xnvi/action_2_poor/doc/datasheet/lcd_pin_def.jpg

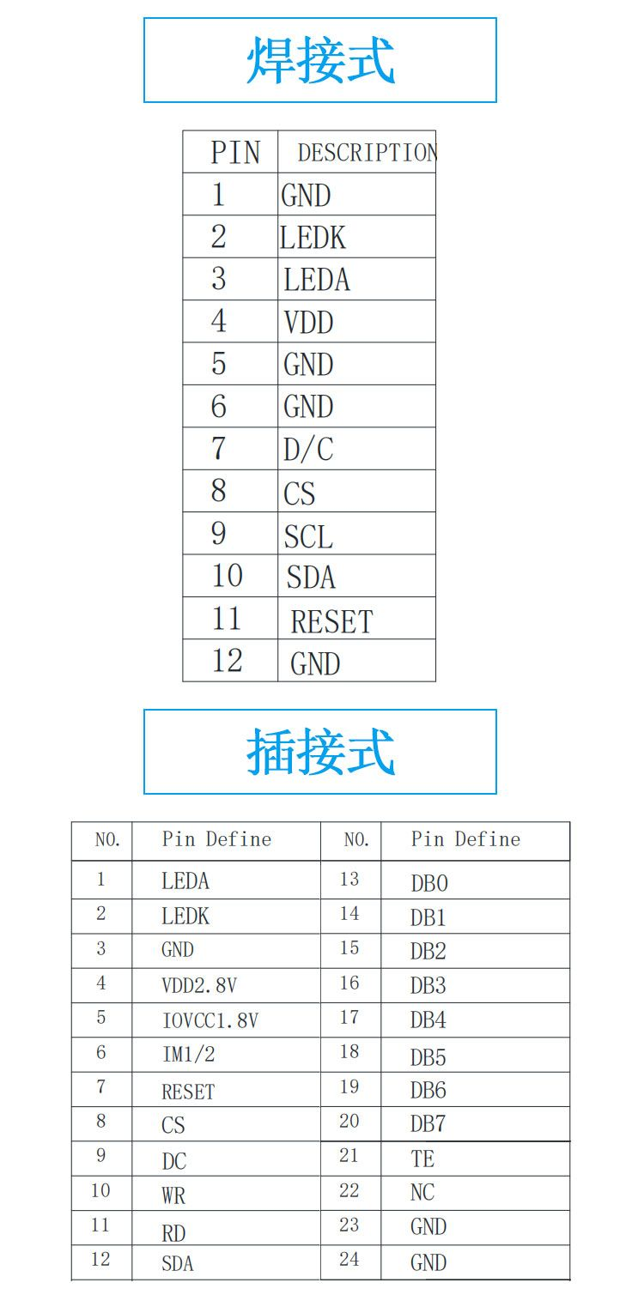
doc/datasheet/lcd_pin_def.jpg
