xnvi/action_2_poor/doc/datasheet/lcd_screen_struct.jpg

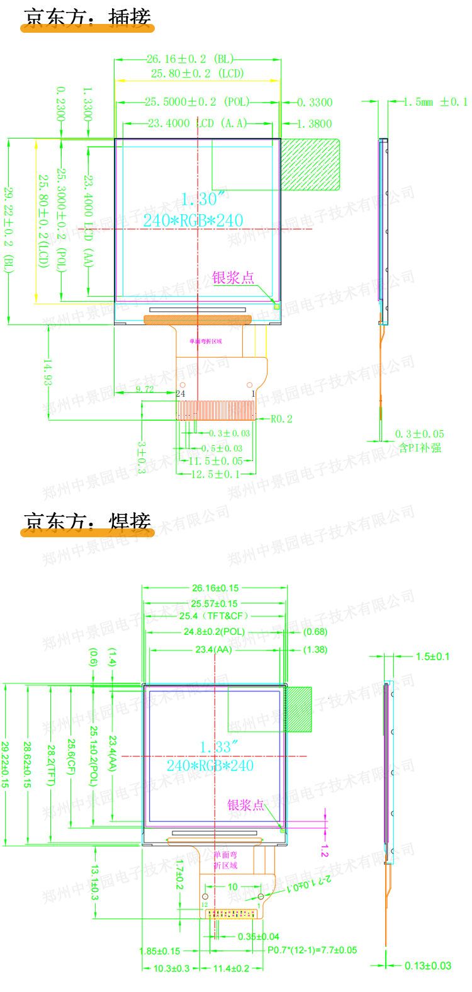
doc/datasheet/lcd_screen_struct.jpg
