xnvi/action_2_poor/doc/datasheet/ov5640_fov67.jpg

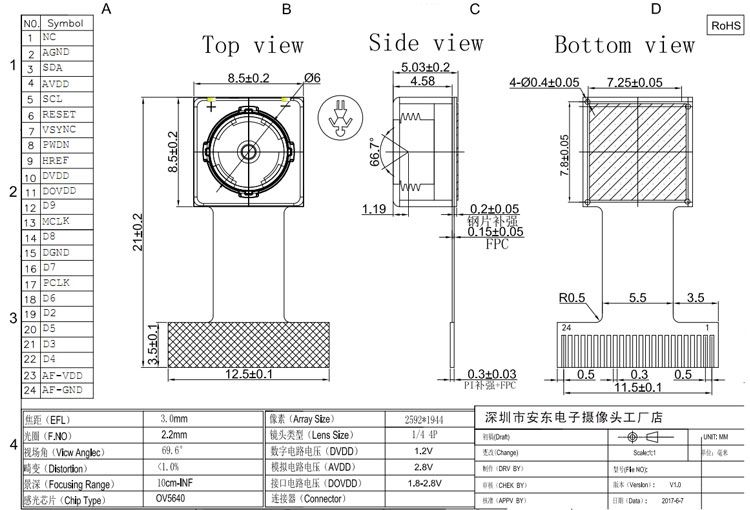
doc/datasheet/ov5640_fov67.jpg
