xnvi/action_2_poor/doc/datasheet/ov5640_fov96.jpg

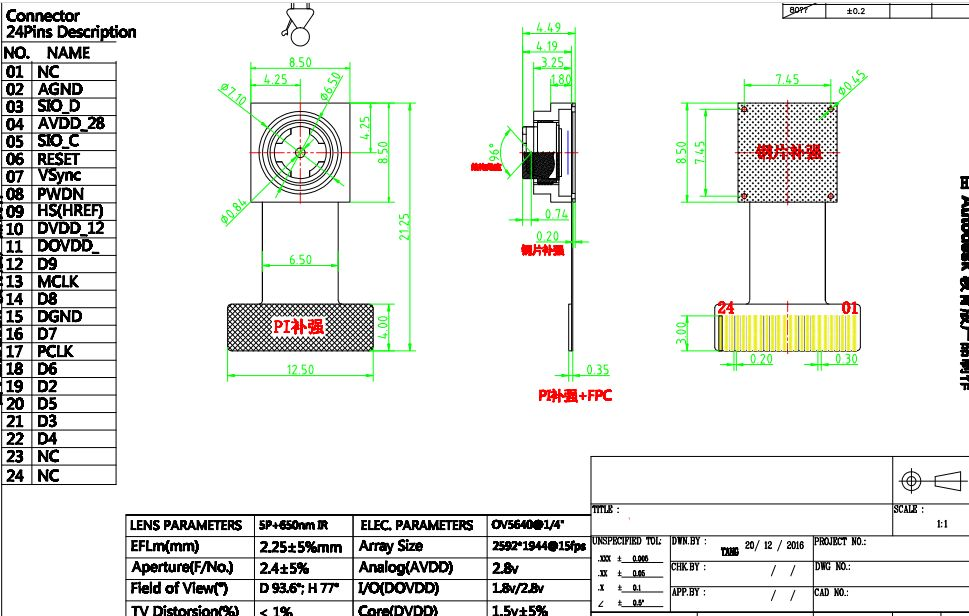
doc/datasheet/ov5640_fov96.jpg
