xnvi/action_2_poor/doc/datasheet/touch_screen.jpg

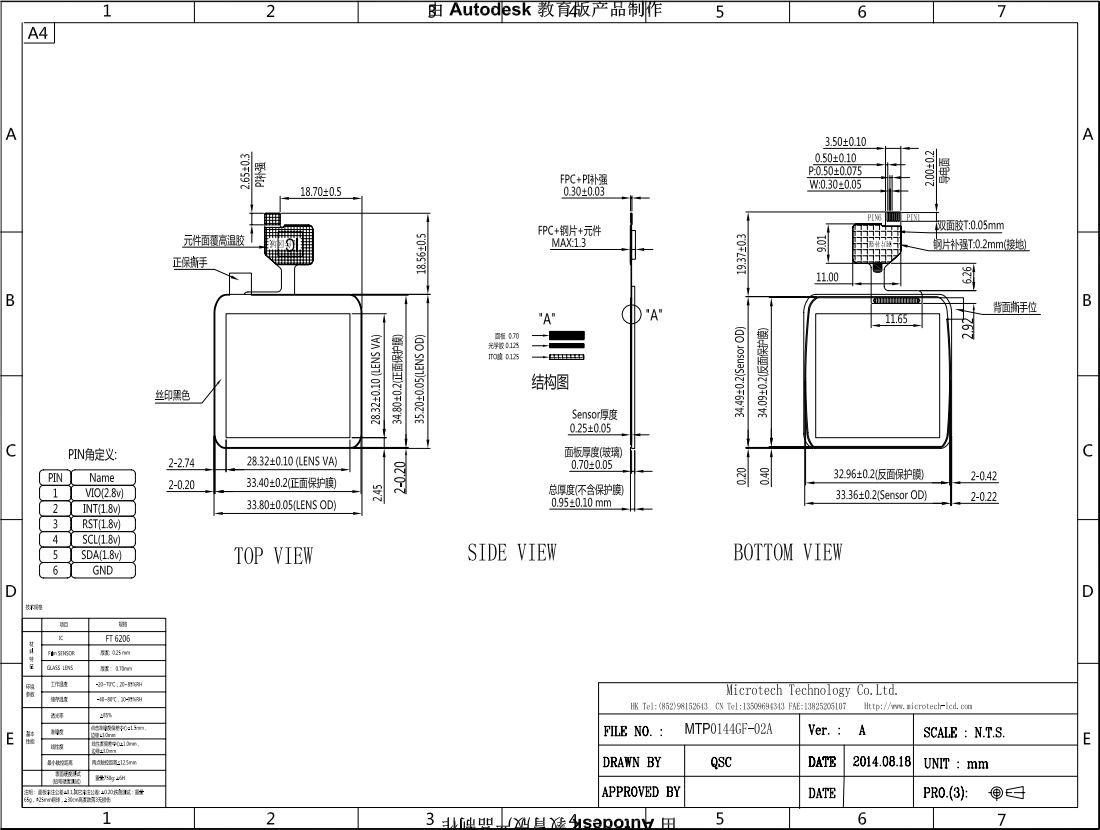
doc/datasheet/touch_screen.jpg
