xnvi/action_2_poor/software/app/camera/src/himpp_venc.c

/******************************************************************************

  Copyright (C), 2017, Hisilicon Tech. Co., Ltd.

 ******************************************************************************
  File Name     : sample_comm_venc.c
  Version       : Initial Draft
  Author        : Hisilicon multimedia software group
  Created       : 2017
  Description   :
******************************************************************************/


#ifdef __cplusplus
#if __cplusplus
extern "C" {
#endif
#endif /* End of #ifdef __cplusplus */

#include <stdio.h>
#include <stdlib.h>
#include <string.h>
#include <sys/types.h>
#include <sys/stat.h>
#include <sys/ioctl.h>
#include <sys/poll.h>
#include <sys/time.h>
#include <sys/select.h>
#include <fcntl.h>
#include <errno.h>
#include <pthread.h>
#include <math.h>
#include <unistd.h>
#include <signal.h>
#include <sys/prctl.h>

#include "himpp.h"

// my edit
#include "camera_himpp_config.h"

const HI_U8 g_SOI[2] = {0xFF, 0xD8};
const HI_U8 g_EOI[2] = {0xFF, 0xD9};
static pthread_t gs_VencPid;
static pthread_t gs_VencQpmapPid;
static HIMPP_VENC_GETSTREAM_PARA_S gs_stPara;
static HIMPP_VENC_QPMAP_SENDFRAME_PARA_S stQpMapSendFramePara;

static HI_S32 gs_s32SnapCnt = 0;
HI_CHAR* DstBuf = NULL;
#define TEMP_BUF_LEN 8
#define MAX_THM_SIZE (64*1024)

// my edit
extern HI_S32 get_hisi_video_frame(VENC_CHN VencChn, VENC_STREAM_S* pstStream);

#ifdef __READ_ALL_FILE__
static HI_S32 FileTrans_GetThmFromJpg(HI_CHAR* JPGPath, HI_U32* DstSize)
{
    HI_S32 s32RtnVal = 0;
    FILE* fpJpg = NULL;
    HI_CHAR tempbuf[TEMP_BUF_LEN] = {0};
    HI_S32 bufpos = 0;
    HI_CHAR startflag[2] = {0xff, 0xd8};
    HI_S32 startpos = 0;
    HI_CHAR endflag[2] = {0xff, 0xd9};
    HI_S32 endpos = 0;
    fpJpg = fopen(JPGPath, "rb");
    HI_CHAR* pszFile = NULL;
    HI_S32 fd = 0;
    HI_S32 s32I = 0;
    struct stat stStat;
    memset(&stStat, 0, sizeof(struct stat));
    if (NULL == fpJpg)
    {
        printf("file %s not exist!\n", JPGPath);
        return HI_FAILURE;
    }
    else
    {
        fd = fileno(fpJpg);
        fstat(fd, &stStat);
        pszFile = (HI_CHAR*)malloc(stStat.st_size);
        if ((NULL == pszFile) || (stStat.st_size < 6))
        {
            fclose(fpJpg);
            printf("memory malloc fail!\n");
            return HI_FAILURE;
        }

        if (fread(pszFile, stStat.st_size , 1, fpJpg) <= 0)
        {
            fclose(fpJpg);
            free(pszFile);
            printf("fread jpeg src fail!\n");
            return HI_FAILURE;
        }

        fclose(fpJpg);
        HI_U16 u16THMLen = 0;
        u16THMLen = (pszFile[4] << 8) + pszFile[5];
        while (s32I < stStat.st_size)
        {
            tempbuf[bufpos] = pszFile[s32I++];
            if (bufpos > 0)
            {
                if (0 == memcmp(tempbuf + bufpos - 1, startflag, sizeof(startflag)))
                {
                    startpos = s32I - 2;
                    if (startpos < 0)
                    {
                        startpos = 0;
                    }
                }
                if (0 == memcmp(tempbuf + bufpos - 1, endflag, sizeof(endflag)))
                {
                    if (u16THMLen == s32I)
                    {
                        endpos = s32I;
                        break;
                    }
                    else
                    {
                        endpos = s32I;
                        break;
                    }
                }
            }
            bufpos++;
            if (bufpos == (TEMP_BUF_LEN - 1))
            {
                if (tempbuf[bufpos - 1] != 0xFF)
                {
                    bufpos = 0;
                }

            }
            else if (bufpos > (TEMP_BUF_LEN - 1))
            {
                bufpos = 0;
            }

        }

    }
    if (endpos - startpos <= 0)
    {
        free(pszFile);
        printf("get .thm 11 fail!\n");
        return HI_FAILURE;
    }

    if (endpos - startpos >= stStat.st_size)
    {
        free(pszFile);
        printf("NO DCF info, get .thm 22 fail!\n");
        return HI_FAILURE;
    }

    HI_CHAR* temp = pszFile + startpos;
    if(MAX_THM_SIZE < (endpos - startpos))
    {
        printf("Thm is too large than MAX_THM_SIZE, get .thm 33 fail!\n");
        return HI_FAILURE;
    }

    HI_CHAR* cDstBuf = (HI_CHAR*)malloc(endpos - startpos);
    if (NULL == cDstBuf)
    {
        printf("memory malloc fail!\n");
        return HI_FAILURE;
    }

    memcpy(cDstBuf, temp, endpos - startpos);

    DstBuf = cDstBuf;
    *DstSize = endpos - startpos;
    free(pszFile);

    return HI_SUCCESS;
}

#else
static HI_S32 FileTrans_GetThmFromJpg(HI_CHAR* JPGPath, HI_U32* DstSize)
{
    HI_CHAR tempbuf[TEMP_BUF_LEN] = {0};
    HI_S32 bufpos = 0;
    HI_CHAR startflag[2] = {0xff, 0xd8};
    HI_S32 startpos = 0;
    HI_CHAR endflag[2] = {0xff, 0xd9};
    HI_S32 endpos = 0;
    HI_BOOL bStartMatch = HI_FALSE;

    HI_S32 fd = 0;
    struct stat stStat;
    memset(&stStat, 0, sizeof(struct stat));

    FILE* fpJpg = NULL;
    fpJpg = fopen(JPGPath, "rb");
    if (NULL == fpJpg)
    {
        printf("file %s not exist!\n", JPGPath);
        return HI_FAILURE;
    }
    else
    {
        fd = fileno(fpJpg);
        fstat(fd, &stStat);

        while (!feof(fpJpg))
        {
            tempbuf[bufpos]=getc(fpJpg);
            if (bufpos > 0)
            {
                if (0 == memcmp(tempbuf + bufpos - 1, startflag, sizeof(startflag)))
                {
                    startpos = ftell(fpJpg)-2;
                    if (startpos < 0)
                    {
                        startpos = 0;
                    }
                    bStartMatch = HI_TRUE;
                }
                if (0 == memcmp(tempbuf + bufpos - 1, endflag, sizeof(endflag)))
                {
                    endpos = ftell(fpJpg);
                    if(HI_TRUE == bStartMatch)
                    {
                        break;
                    }
                }
            }
            bufpos++;

            if (bufpos == (TEMP_BUF_LEN - 1))
            {
                if (tempbuf[bufpos - 1] != 0xFF)
                {
                    bufpos = 0;
                }
            }
            else if (bufpos > (TEMP_BUF_LEN - 1))
            {
                if (tempbuf[bufpos -1] == 0xFF)
                {
                    tempbuf[0] = 0xFF;
                    bufpos = 1;
                }
                else
                {
                    bufpos = 0;
                }
            }
        }
    }

    if (endpos - startpos <= 0)
    {
        printf("get .thm 11 fail!\n");
        fclose(fpJpg);
        return HI_FAILURE;
    }

    if (endpos - startpos > MAX_THM_SIZE)
    {
        printf("Thm is too large than MAX_THM_SIZE, get .thm 22 fail!\n");
        fclose(fpJpg);
        return HI_FAILURE;
    }

    if (endpos - startpos >= stStat.st_size)
    {
        printf("NO DCF info, get .thm 33 fail!\n");
        fclose(fpJpg);
        return HI_FAILURE;
    }

    HI_CHAR* cDstBuf = (HI_CHAR*)malloc(endpos - startpos);
    if (NULL == cDstBuf)
    {
        printf("memory malloc fail!\n");
        fclose(fpJpg);
        return HI_FAILURE;
    }

    fseek(fpJpg, (long)startpos, SEEK_SET);
    *DstSize = fread(cDstBuf,1,endpos-startpos,fpJpg);
    if(*DstSize != (endpos - startpos))
    {
        free(cDstBuf);
        printf("fread fail!\n");
        fclose(fpJpg);
        return HI_FAILURE;
    }

    DstBuf = cDstBuf;
    fclose(fpJpg);

    return HI_SUCCESS;
}
#endif


/******************************************************************************
* funciton : get file postfix according palyload_type.
******************************************************************************/
HI_S32 HIMPP_VENC_GetFilePostfix(PAYLOAD_TYPE_E enPayload, char* szFilePostfix)
{
    if (PT_H264 == enPayload)
    {
        strcpy(szFilePostfix, ".h264");
    }
    else if (PT_H265 == enPayload)
    {
        strcpy(szFilePostfix, ".h265");
    }
    else if (PT_JPEG == enPayload)
    {
        strcpy(szFilePostfix, ".jpg");
    }
    else if (PT_MJPEG == enPayload)
    {
        strcpy(szFilePostfix, ".mjp");
    }
    else
    {
        HIMPP_PRT("payload type err!\n");
        return HI_FAILURE;
    }
    return HI_SUCCESS;
}


HI_S32 HIMPP_VENC_GetGopAttr(VENC_GOP_MODE_E enGopMode,VENC_GOP_ATTR_S *pstGopAttr)
{
    switch(enGopMode)
    {
        case VENC_GOPMODE_NORMALP:
            pstGopAttr->enGopMode  = VENC_GOPMODE_NORMALP;
            pstGopAttr->stNormalP.s32IPQpDelta = 2;
        break;
        case VENC_GOPMODE_SMARTP:
            pstGopAttr->enGopMode  = VENC_GOPMODE_SMARTP;
            pstGopAttr->stSmartP.s32BgQpDelta  = 4;
            pstGopAttr->stSmartP.s32ViQpDelta  = 2;
            pstGopAttr->stSmartP.u32BgInterval =  90;
        break;

        case VENC_GOPMODE_DUALP:
            pstGopAttr->enGopMode  = VENC_GOPMODE_DUALP;
            pstGopAttr->stDualP.s32IPQpDelta  = 4;
            pstGopAttr->stDualP.s32SPQpDelta  = 2;
            pstGopAttr->stDualP.u32SPInterval = 3;
        break;

        case VENC_GOPMODE_BIPREDB:
            pstGopAttr->enGopMode  = VENC_GOPMODE_BIPREDB;
            pstGopAttr->stBipredB.s32BQpDelta  = -2;
            pstGopAttr->stBipredB.s32IPQpDelta = 3;
            pstGopAttr->stBipredB.u32BFrmNum   = 2;
        break;

        default:
            HIMPP_PRT("not support the gop mode !\n");
            return HI_FAILURE;
        break;
    }
    return HI_SUCCESS;
}


HI_S32 HIMPP_VENC_Getdcfinfo(char* SrcJpgPath, char* DstThmPath)
{
    HI_S32 s32RtnVal = HI_SUCCESS;
    HI_CHAR JPGSrcPath[FILE_NAME_LEN] = {0};
    HI_CHAR JPGDesPath[FILE_NAME_LEN] = {0};
    HI_U32 DstSize = 0;
    snprintf(JPGSrcPath, sizeof(JPGSrcPath), "%s", SrcJpgPath);
    snprintf(JPGDesPath, sizeof(JPGDesPath), "%s", DstThmPath);

    s32RtnVal = FileTrans_GetThmFromJpg(JPGSrcPath, &DstSize);
    if ((HI_SUCCESS != s32RtnVal) || (0 == DstSize))
    {
        printf("fail to get thm\n");
        return HI_FAILURE;
    }

    FILE* fpTHM = fopen(JPGDesPath, "w");
    if (HI_NULL == fpTHM)
    {
        printf("file to create file %s\n", JPGDesPath);
        return HI_FAILURE;
    }

    HI_U32 u32WritenSize = 0;
    while (u32WritenSize < DstSize)
    {
        s32RtnVal = fwrite(DstBuf + u32WritenSize, 1, DstSize, fpTHM);
        if (s32RtnVal <= 0)
        {
            printf("fail to wirte file, rtn=%d\n", s32RtnVal);
            break;
        }

        u32WritenSize += s32RtnVal;
    }

    if (fpTHM)
    {
        fclose(fpTHM);
        fpTHM = 0;
    }

    if(NULL != DstBuf)
    {
        free(DstBuf);
        DstBuf = NULL;
    }

    return 0;
}



/******************************************************************************
* funciton : save stream
******************************************************************************/
HI_S32 HIMPP_VENC_SaveStream(FILE* pFd, VENC_STREAM_S* pstStream)
{
    HI_S32 i;

    for (i = 0; i < pstStream->u32PackCount; i++)
    {
        fwrite(pstStream->pstPack[i].pu8Addr + pstStream->pstPack[i].u32Offset,
               pstStream->pstPack[i].u32Len - pstStream->pstPack[i].u32Offset, 1, pFd);

        fflush(pFd);
    }

    return HI_SUCCESS;
}


/******************************************************************************
* funciton : the process of physical address retrace
******************************************************************************/
HI_S32 HIMPP_VENC_SaveStream_PhyAddr(FILE* pFd, VENC_STREAM_BUF_INFO_S *pstStreamBuf, VENC_STREAM_S* pstStream)
{
    HI_U32 i,j;
    HI_U64 u64SrcPhyAddr;
    HI_U32 u32Left;
    HI_S32 s32Ret = 0;

    for(i=0; i<pstStream->u32PackCount; i++)
    {
        for(j=0; j<MAX_TILE_NUM; j++)
        {
            if((pstStream->pstPack[i].u64PhyAddr > pstStreamBuf->u64PhyAddr[j])&&\
                (pstStream->pstPack[i].u64PhyAddr <= pstStreamBuf->u64PhyAddr[j]+pstStreamBuf->u64BufSize[j]))
                break;
        }

        if(pstStream->pstPack[i].u64PhyAddr + pstStream->pstPack[i].u32Len >=
                pstStreamBuf->u64PhyAddr[j] + pstStreamBuf->u64BufSize[j])
        {
            if (pstStream->pstPack[i].u64PhyAddr + pstStream->pstPack[i].u32Offset >=
                pstStreamBuf->u64PhyAddr[j] + pstStreamBuf->u64BufSize[j])
            {
                /* physical address retrace in offset segment */
                u64SrcPhyAddr = pstStreamBuf->u64PhyAddr[j] +
                                ((pstStream->pstPack[i].u64PhyAddr + pstStream->pstPack[i].u32Offset) -
                                (pstStreamBuf->u64PhyAddr[j] + pstStreamBuf->u64BufSize[j]));

                s32Ret = fwrite ((void *)(HI_UL)u64SrcPhyAddr, pstStream->pstPack[i].u32Len - pstStream->pstPack[i].u32Offset, 1, pFd);
                if(s32Ret<0)
                {
                    HIMPP_PRT("fwrite err %d\n", s32Ret);
                    return s32Ret;
                }
            }
            else
            {
                /* physical address retrace in data segment */
                u32Left = (pstStreamBuf->u64PhyAddr[j] + pstStreamBuf->u64BufSize[j]) - pstStream->pstPack[i].u64PhyAddr;

                s32Ret = fwrite((void *)(HI_UL)(pstStream->pstPack[i].u64PhyAddr + pstStream->pstPack[i].u32Offset),
                             u32Left - pstStream->pstPack[i].u32Offset, 1, pFd);
                if(s32Ret<0)
                {
                    HIMPP_PRT("fwrite err %d\n", s32Ret);
                    return s32Ret;
                }

                s32Ret = fwrite((void *)(HI_UL)pstStreamBuf->u64PhyAddr[j], pstStream->pstPack[i].u32Len - u32Left, 1, pFd);
                if(s32Ret<0)
                {
                    HIMPP_PRT("fwrite err %d\n", s32Ret);
                    return s32Ret;
                }
            }
        }
        else
        {
            /* physical address retrace does not happen */
            s32Ret = fwrite ((void *)(HI_UL)(pstStream->pstPack[i].u64PhyAddr + pstStream->pstPack[i].u32Offset),
                          pstStream->pstPack[i].u32Len - pstStream->pstPack[i].u32Offset, 1, pFd);
            if(s32Ret<0)
            {
                HIMPP_PRT("fwrite err %d\n", s32Ret);
                return s32Ret;
            }
        }
            fflush(pFd);
    }
    return HI_SUCCESS;
}

HI_S32 HIMPP_VENC_CloseReEncode(VENC_CHN VencChn)
{
    HI_S32 s32Ret;
    VENC_RC_PARAM_S stRcParam;
    VENC_CHN_ATTR_S stChnAttr;

    s32Ret = HI_MPI_VENC_GetChnAttr(VencChn,&stChnAttr);
    if (HI_SUCCESS != s32Ret)
    {
        HIMPP_PRT("GetChnAttr failed!\n");
        return HI_FAILURE;
    }

    s32Ret = HI_MPI_VENC_GetRcParam(VencChn,&stRcParam);
    if (HI_SUCCESS != s32Ret)
    {
        HIMPP_PRT("GetRcParam failed!\n");
        return HI_FAILURE;
    }

    if(VENC_RC_MODE_H264CBR == stChnAttr.stRcAttr.enRcMode)
    {
        stRcParam.stParamH264Cbr.s32MaxReEncodeTimes = 0;
    }
    else if(VENC_RC_MODE_H264VBR == stChnAttr.stRcAttr.enRcMode)
    {
        stRcParam.stParamH264Vbr.s32MaxReEncodeTimes = 0;
    }
    else if(VENC_RC_MODE_H265CBR == stChnAttr.stRcAttr.enRcMode)
    {
        stRcParam.stParamH264Cbr.s32MaxReEncodeTimes = 0;
    }
    else if(VENC_RC_MODE_H265VBR == stChnAttr.stRcAttr.enRcMode)
    {
        stRcParam.stParamH264Vbr.s32MaxReEncodeTimes = 0;
    }
    else
    {
        return HI_SUCCESS;
    }
    s32Ret = HI_MPI_VENC_SetRcParam(VencChn,&stRcParam);
    if (HI_SUCCESS != s32Ret)
    {
        HIMPP_PRT("SetRcParam failed!\n");
        return HI_FAILURE;
    }
    return HI_SUCCESS;
}

HI_S32 HIMPP_VENC_Creat(VENC_CHN VencChn, PAYLOAD_TYPE_E enType,  PIC_SIZE_E enSize, HIMPP_RC_E enRcMode, HI_U32  u32Profile, HI_BOOL bRcnRefShareBuf,VENC_GOP_ATTR_S *pstGopAttr)
{
    HI_S32 s32Ret;
    SIZE_S stPicSize;
    VENC_CHN_ATTR_S        stVencChnAttr;
    VENC_ATTR_JPEG_S       stJpegAttr;
    HIMPP_VI_CONFIG_S     stViConfig;
    HI_U32                 u32FrameRate;
    HI_U32                 u32StatTime;
    HI_U32                 u32Gop = 30;

    s32Ret = HIMPP_SYS_GetPicSize( enSize, &stPicSize);
    if (HI_SUCCESS != s32Ret)
    {
        HIMPP_PRT("Get picture size failed!\n");
        return HI_FAILURE;
    }

    HIMPP_VI_GetSensorInfo(&stViConfig);
    if(HIMPP_SNS_TYPE_BUTT == stViConfig.astViInfo[0].stSnsInfo.enSnsType)
    {
        HIMPP_PRT("Not set SENSOR%d_TYPE !\n",0);
        return HI_FALSE;
    }
    s32Ret = HIMPP_VI_GetFrameRateBySensor(stViConfig.astViInfo[0].stSnsInfo.enSnsType, &u32FrameRate);
    if (HI_SUCCESS != s32Ret)
    {
        HIMPP_PRT("HIMPP_VI_GetFrameRateBySensor failed!\n");
        return s32Ret;
    }

    /******************************************
     step 1:  Create Venc Channel
    ******************************************/
    stVencChnAttr.stVencAttr.enType          = enType;
    stVencChnAttr.stVencAttr.u32MaxPicWidth  = stPicSize.u32Width;
    stVencChnAttr.stVencAttr.u32MaxPicHeight = stPicSize.u32Height;
    stVencChnAttr.stVencAttr.u32PicWidth     = stPicSize.u32Width;/*the picture width*/
    stVencChnAttr.stVencAttr.u32PicHeight    = stPicSize.u32Height;/*the picture height*/

    if (enType == PT_MJPEG || enType == PT_JPEG)
    {
        stVencChnAttr.stVencAttr.u32BufSize      = ALIGN_UP(stPicSize.u32Width, 16) * ALIGN_UP(stPicSize.u32Height, 16);
    }
    else
    {
        stVencChnAttr.stVencAttr.u32BufSize      = ALIGN_UP(stPicSize.u32Width * stPicSize.u32Height * 3 / 4, 64);/*stream buffer size*/
    }
    stVencChnAttr.stVencAttr.u32Profile      = u32Profile;
    stVencChnAttr.stVencAttr.bByFrame        = HI_TRUE;/*get stream mode is slice mode or frame mode?*/

    if(VENC_GOPMODE_SMARTP == pstGopAttr->enGopMode)
    {
        u32StatTime = pstGopAttr->stSmartP.u32BgInterval/u32Gop;
    }
    else
    {
        u32StatTime = 1;
    }

    switch (enType)
    {
        case PT_H265:
        {
            if (HIMPP_RC_CBR == enRcMode)
            {
                VENC_H265_CBR_S    stH265Cbr;

                stVencChnAttr.stRcAttr.enRcMode = VENC_RC_MODE_H265CBR;
                stH265Cbr.u32Gop            = u32Gop;
                stH265Cbr.u32StatTime       = u32StatTime; /* stream rate statics time(s) */
                stH265Cbr.u32SrcFrameRate   = u32FrameRate; /* input (vi) frame rate */
                stH265Cbr.fr32DstFrameRate  = u32FrameRate; /* target frame rate */
                switch (enSize)
                {
                    // my edit 目前只使用cbr，这里通过码率设置图像质量
                    case PIC_VGA:
                        stH265Cbr.u32BitRate = (1024 + 512*u32FrameRate/30) * g_br_list[g_br_index].num/g_br_list[g_br_index].den;
                        break;
                    case PIC_720P:
                        stH265Cbr.u32BitRate = (1024 * 2 + 1024*u32FrameRate/30) * g_br_list[g_br_index].num/g_br_list[g_br_index].den;
                        break;
                    case PIC_1080P:
                        stH265Cbr.u32BitRate = (1024 * 2 + 2048*u32FrameRate/30) * g_br_list[g_br_index].num/g_br_list[g_br_index].den;
                        break;
                    case PIC_2592x1944:
                        stH265Cbr.u32BitRate = (1024 * 3 + 3072*u32FrameRate/30) * g_br_list[g_br_index].num/g_br_list[g_br_index].den;
                        break;
                    case PIC_3840x2160:
                        stH265Cbr.u32BitRate = (1024 * 5  + 5120*u32FrameRate/30) * g_br_list[g_br_index].num/g_br_list[g_br_index].den;
                        break;
                    default : //other small resolution
                        stH265Cbr.u32BitRate = 256;
                        break;
                }
                memcpy(&stVencChnAttr.stRcAttr.stH265Cbr, &stH265Cbr, sizeof(VENC_H265_CBR_S));
            }
            else if (HIMPP_RC_FIXQP == enRcMode)
            {
                VENC_H265_FIXQP_S    stH265FixQp;

                stVencChnAttr.stRcAttr.enRcMode = VENC_RC_MODE_H265FIXQP;
                stH265FixQp.u32Gop              = 30;
                stH265FixQp.u32SrcFrameRate     = u32FrameRate;
                stH265FixQp.fr32DstFrameRate    = u32FrameRate;
                stH265FixQp.u32IQp              = 25;
                stH265FixQp.u32PQp              = 30;
                stH265FixQp.u32BQp              = 32;
                memcpy(&stVencChnAttr.stRcAttr.stH265FixQp, &stH265FixQp, sizeof(VENC_H265_FIXQP_S));
            }
            else if (HIMPP_RC_VBR == enRcMode)
            {
                VENC_H265_VBR_S    stH265Vbr;

                stVencChnAttr.stRcAttr.enRcMode = VENC_RC_MODE_H265VBR;
                stH265Vbr.u32Gop           = u32Gop;
                stH265Vbr.u32StatTime      = u32StatTime;
                stH265Vbr.u32SrcFrameRate  = u32FrameRate;
                stH265Vbr.fr32DstFrameRate = u32FrameRate;
                switch (enSize)
                {
                    case PIC_VGA:
                        stH265Vbr.u32MaxBitRate = 1024 + 512*u32FrameRate/30;
                        break;
                    case PIC_720P:
                        stH265Vbr.u32MaxBitRate = 1024 * 2 + 1024*u32FrameRate/30;
                        break;
                    case PIC_1080P:
                        stH265Vbr.u32MaxBitRate = 1024 * 2 + 2048*u32FrameRate/30;
                        break;
                    case PIC_2592x1944:
                        stH265Vbr.u32MaxBitRate = 1024 * 3 + 3072*u32FrameRate/30;
                        break;
                    default :
                        stH265Vbr.u32MaxBitRate    = 1024 * 15 + 2048*u32FrameRate/30;
                        break;
                }
                memcpy(&stVencChnAttr.stRcAttr.stH265Vbr, &stH265Vbr, sizeof(VENC_H265_VBR_S));
            }
            else if(HIMPP_RC_AVBR == enRcMode)
            {
                VENC_H265_AVBR_S    stH265AVbr;

                stVencChnAttr.stRcAttr.enRcMode = VENC_RC_MODE_H265AVBR;
                stH265AVbr.u32Gop         = u32Gop;
                stH265AVbr.u32StatTime    = u32StatTime;
                stH265AVbr.u32SrcFrameRate  = u32FrameRate;
                stH265AVbr.fr32DstFrameRate = u32FrameRate;
                switch (enSize)
                {
                    case PIC_VGA:
                        stH265AVbr.u32MaxBitRate = 1024 + 512*u32FrameRate/30;
                        break;
                    case PIC_720P:
                        stH265AVbr.u32MaxBitRate = 1024 * 2 + 1024*u32FrameRate/30;
                        break;
                    case PIC_1080P:
                        stH265AVbr.u32MaxBitRate = 1024 * 2 + 2048*u32FrameRate/30;
                        break;
                    case PIC_2592x1944:
                        stH265AVbr.u32MaxBitRate = 1024 * 3 + 3072*u32FrameRate/30;
                        break;
                    case PIC_3840x2160:
                        stH265AVbr.u32MaxBitRate = 1024 * 5  + 5120*u32FrameRate/30;
                        break;
                    default :
                        stH265AVbr.u32MaxBitRate    = 1024 * 15 + 2048*u32FrameRate/30;
                        break;
                }
                memcpy(&stVencChnAttr.stRcAttr.stH265AVbr, &stH265AVbr, sizeof(VENC_H265_AVBR_S));
            }
            else if(HIMPP_RC_QVBR == enRcMode)
            {
                VENC_H265_QVBR_S    stH265QVbr;

                stVencChnAttr.stRcAttr.enRcMode = VENC_RC_MODE_H265QVBR;
                stH265QVbr.u32Gop         = u32Gop;
                stH265QVbr.u32StatTime    = u32StatTime;
                stH265QVbr.u32SrcFrameRate  = u32FrameRate;
                stH265QVbr.fr32DstFrameRate = u32FrameRate;
                switch (enSize)
                {
                    case PIC_VGA:
                        stH265QVbr.u32TargetBitRate = 1024 + 512*u32FrameRate/30;
                        break;
                    case PIC_720P:
                        stH265QVbr.u32TargetBitRate= 1024 * 2 + 1024*u32FrameRate/30;
                        break;
                    case PIC_1080P:
                        stH265QVbr.u32TargetBitRate = 1024 * 2 + 2048*u32FrameRate/30;
                        break;
                    case PIC_2592x1944:
                        stH265QVbr.u32TargetBitRate = 1024 * 3 + 3072*u32FrameRate/30;
                        break;
                    case PIC_3840x2160:
                        stH265QVbr.u32TargetBitRate = 1024 * 5  + 5120*u32FrameRate/30;
                        break;
                    case PIC_4000x3000:
                        stH265QVbr.u32TargetBitRate = 1024 * 10 + 5120*u32FrameRate/30;
                        break;
                    case PIC_7680x4320:
                        stH265QVbr.u32TargetBitRate = 1024 * 20 + 5120*u32FrameRate/30;
                        break;
                    default :
                        stH265QVbr.u32TargetBitRate    = 1024 * 15 + 2048*u32FrameRate/30;
                        break;
                }
                memcpy(&stVencChnAttr.stRcAttr.stH265QVbr, &stH265QVbr, sizeof(VENC_H265_QVBR_S));
            }
            else if(HIMPP_RC_CVBR == enRcMode)
            {
                VENC_H265_CVBR_S    stH265CVbr;

                stVencChnAttr.stRcAttr.enRcMode = VENC_RC_MODE_H265CVBR;
                stH265CVbr.u32Gop         = u32Gop;
                stH265CVbr.u32StatTime    = u32StatTime;
                stH265CVbr.u32SrcFrameRate  = u32FrameRate;
                stH265CVbr.fr32DstFrameRate = u32FrameRate;
                stH265CVbr.u32LongTermStatTime  = 1;
                stH265CVbr.u32ShortTermStatTime = u32StatTime;
                switch (enSize)
                {
                    case PIC_VGA:
                        stH265CVbr.u32MaxBitRate = 1024 + 512*u32FrameRate/30;
                        stH265CVbr.u32LongTermMaxBitrate = 1024  + 512*u32FrameRate/30;
                        stH265CVbr.u32LongTermMinBitrate = 256;
                        break;
                    case PIC_720P:
                        stH265CVbr.u32MaxBitRate         = 1024 * 3 + 1024*u32FrameRate/30;
                        stH265CVbr.u32LongTermMaxBitrate = 1024 * 2 + 1024*u32FrameRate/30;
                        stH265CVbr.u32LongTermMinBitrate = 512;
                        break;
                    case PIC_1080P:
                        stH265CVbr.u32MaxBitRate         = 1024 * 2 + 2048*u32FrameRate/30;
                        stH265CVbr.u32LongTermMaxBitrate = 1024 * 2 + 2048*u32FrameRate/30;
                        stH265CVbr.u32LongTermMinBitrate = 1024;
                        break;
                    case PIC_2592x1944:
                        stH265CVbr.u32MaxBitRate         = 1024 * 4 + 3072*u32FrameRate/30;
                        stH265CVbr.u32LongTermMaxBitrate = 1024 * 3 + 3072*u32FrameRate/30;
                        stH265CVbr.u32LongTermMinBitrate = 1024*2;
                        break;
                    case PIC_3840x2160:
                        stH265CVbr.u32MaxBitRate         = 1024 * 8  + 5120*u32FrameRate/30;
                        stH265CVbr.u32LongTermMaxBitrate = 1024 * 5  + 5120*u32FrameRate/30;
                        stH265CVbr.u32LongTermMinBitrate = 1024*3;
                        break;
                    case PIC_4000x3000:
                        stH265CVbr.u32MaxBitRate         = 1024 * 12  + 5120*u32FrameRate/30;
                        stH265CVbr.u32LongTermMaxBitrate = 1024 * 10 + 5120*u32FrameRate/30;
                        stH265CVbr.u32LongTermMinBitrate = 1024*4;
                        break;
                    case PIC_7680x4320:
                        stH265CVbr.u32MaxBitRate         = 1024 * 24  + 5120*u32FrameRate/30;
                        stH265CVbr.u32LongTermMaxBitrate = 1024 * 20 + 5120*u32FrameRate/30;
                        stH265CVbr.u32LongTermMinBitrate = 1024*6;
                        break;
                    default :
                        stH265CVbr.u32MaxBitRate         = 1024 * 24  + 5120*u32FrameRate/30;
                        stH265CVbr.u32LongTermMaxBitrate = 1024 * 15 + 2048*u32FrameRate/30;
                        stH265CVbr.u32LongTermMinBitrate = 1024*5;
                        break;
                }
                memcpy(&stVencChnAttr.stRcAttr.stH265CVbr, &stH265CVbr, sizeof(VENC_H265_CVBR_S));
            }
            else if(HIMPP_RC_QPMAP == enRcMode)
            {
                VENC_H265_QPMAP_S    stH265QpMap;

                stVencChnAttr.stRcAttr.enRcMode = VENC_RC_MODE_H265QPMAP;
                stH265QpMap.u32Gop           = u32Gop;
                stH265QpMap.u32StatTime      = u32StatTime;
                stH265QpMap.u32SrcFrameRate  = u32FrameRate;
                stH265QpMap.fr32DstFrameRate = u32FrameRate;
                stH265QpMap.enQpMapMode      = VENC_RC_QPMAP_MODE_MEANQP;
                memcpy(&stVencChnAttr.stRcAttr.stH265QpMap, &stH265QpMap, sizeof(VENC_H265_QPMAP_S));
            }
            else
            {
                HIMPP_PRT("%s,%d,enRcMode(%d) not support\n",__FUNCTION__,__LINE__,enRcMode);
                return HI_FAILURE;
            }
            stVencChnAttr.stVencAttr.stAttrH265e.bRcnRefShareBuf = bRcnRefShareBuf;
        }
        break;
        case PT_H264:
        {
            if (HIMPP_RC_CBR == enRcMode)
            {
                VENC_H264_CBR_S    stH264Cbr;

                stVencChnAttr.stRcAttr.enRcMode = VENC_RC_MODE_H264CBR;
                stH264Cbr.u32Gop                = u32Gop; /*the interval of IFrame*/
                stH264Cbr.u32StatTime           = u32StatTime; /* stream rate statics time(s) */
                stH264Cbr.u32SrcFrameRate       = u32FrameRate; /* input (vi) frame rate */
                stH264Cbr.fr32DstFrameRate      = u32FrameRate; /* target frame rate */
                switch (enSize)
                {
                    // my edit 目前只使用cbr，这里通过码率设置图像质量
                    case PIC_VGA:
                        stH264Cbr.u32BitRate = (1024 + 512*u32FrameRate/30) * g_br_list[g_br_index].num/g_br_list[g_br_index].den;
                        break;
                    case PIC_720P:
                        stH264Cbr.u32BitRate = (1024 * 2  + 1024*u32FrameRate/30) * g_br_list[g_br_index].num/g_br_list[g_br_index].den;
                        break;
                    case PIC_1080P:
                        stH264Cbr.u32BitRate = (1024 * 2  + 2048*u32FrameRate/30) * g_br_list[g_br_index].num/g_br_list[g_br_index].den;
                        break;
                    case PIC_2592x1944:
                        stH264Cbr.u32BitRate = (1024 * 3  + 3072*u32FrameRate/30) * g_br_list[g_br_index].num/g_br_list[g_br_index].den;
                        break;
                    case PIC_3840x2160:
                        stH264Cbr.u32BitRate = (1024 * 5 + 5120*u32FrameRate/30) * g_br_list[g_br_index].num/g_br_list[g_br_index].den;
                        break;
                    default :  //other small resolution
                        stH264Cbr.u32BitRate = 512;
                        break;
                }

                memcpy(&stVencChnAttr.stRcAttr.stH264Cbr, &stH264Cbr, sizeof(VENC_H264_CBR_S));
            }
            else if (HIMPP_RC_FIXQP == enRcMode)
            {
                VENC_H264_FIXQP_S    stH264FixQp;

                stVencChnAttr.stRcAttr.enRcMode = VENC_RC_MODE_H264FIXQP;
                stH264FixQp.u32Gop           = 30;
                stH264FixQp.u32SrcFrameRate  = u32FrameRate;
                stH264FixQp.fr32DstFrameRate = u32FrameRate;
                stH264FixQp.u32IQp           = 25;
                stH264FixQp.u32PQp           = 30;
                stH264FixQp.u32BQp           = 32;
                memcpy(&stVencChnAttr.stRcAttr.stH264FixQp, &stH264FixQp, sizeof(VENC_H264_FIXQP_S));
            }
            else if (HIMPP_RC_VBR == enRcMode)
            {
                VENC_H264_VBR_S    stH264Vbr;

                stVencChnAttr.stRcAttr.enRcMode = VENC_RC_MODE_H264VBR;
                stH264Vbr.u32Gop           = u32Gop;
                stH264Vbr.u32StatTime      = u32StatTime;
                stH264Vbr.u32SrcFrameRate  = u32FrameRate;
                stH264Vbr.fr32DstFrameRate = u32FrameRate;
                switch (enSize)
                {
                    case PIC_VGA:
                        stH264Vbr.u32MaxBitRate = 1024 + 512*u32FrameRate/30;
                        break;
                    case PIC_720P:
                        stH264Vbr.u32MaxBitRate = 1024 * 2   + 1024*u32FrameRate/30;
                        break;
                    case PIC_1080P:
                        stH264Vbr.u32MaxBitRate = 1024 * 2   + 2048*u32FrameRate/30;
                        break;
                    case PIC_2592x1944:
                        stH264Vbr.u32MaxBitRate = 1024 * 3   + 3072*u32FrameRate/30;
                        break;
                    case PIC_3840x2160:
                        stH264Vbr.u32MaxBitRate = 1024 * 5   + 5120*u32FrameRate/30;
                        break;
                    default :
                        stH264Vbr.u32MaxBitRate = 1024 * 15  + 2048*u32FrameRate/30;
                        break;
                }
                memcpy(&stVencChnAttr.stRcAttr.stH264Vbr, &stH264Vbr, sizeof(VENC_H264_VBR_S));
            }
            else if (HIMPP_RC_AVBR == enRcMode)
            {
                VENC_H264_VBR_S    stH264AVbr;

                stVencChnAttr.stRcAttr.enRcMode = VENC_RC_MODE_H264AVBR;
                stH264AVbr.u32Gop           = u32Gop;
                stH264AVbr.u32StatTime      = u32StatTime;
                stH264AVbr.u32SrcFrameRate  = u32FrameRate;
                stH264AVbr.fr32DstFrameRate = u32FrameRate;
                switch (enSize)
                {
                    case PIC_VGA:
                        stH264AVbr.u32MaxBitRate = 1024 + 512*u32FrameRate/30;
                        break;
                    case PIC_720P:
                        stH264AVbr.u32MaxBitRate = 1024 * 2   + 1024*u32FrameRate/30;
                        break;
                    case PIC_1080P:
                        stH264AVbr.u32MaxBitRate = 1024 * 2   + 2048*u32FrameRate/30;
                        break;
                    case PIC_2592x1944:
                        stH264AVbr.u32MaxBitRate = 1024 * 3   + 3072*u32FrameRate/30;
                        break;
                    case PIC_3840x2160:
                        stH264AVbr.u32MaxBitRate = 1024 * 5   + 5120*u32FrameRate/30;
                        break;
                    case PIC_4000x3000:
                        stH264AVbr.u32MaxBitRate = 1024 * 10  + 5120*u32FrameRate/30;
                        break;
                    case PIC_7680x4320:
                        stH264AVbr.u32MaxBitRate = 1024 * 20  + 5120*u32FrameRate/30;
                        break;
                    default :
                        stH264AVbr.u32MaxBitRate = 1024 * 15  + 2048*u32FrameRate/30;
                        break;
                }
                memcpy(&stVencChnAttr.stRcAttr.stH264AVbr, &stH264AVbr, sizeof(VENC_H264_AVBR_S));
            }
            else if (HIMPP_RC_QVBR == enRcMode)
            {
                VENC_H264_QVBR_S    stH264QVbr;

                stVencChnAttr.stRcAttr.enRcMode = VENC_RC_MODE_H264QVBR;
                stH264QVbr.u32Gop           = u32Gop;
                stH264QVbr.u32StatTime      = u32StatTime;
                stH264QVbr.u32SrcFrameRate  = u32FrameRate;
                stH264QVbr.fr32DstFrameRate = u32FrameRate;
                switch (enSize)
                {
                    case PIC_VGA:
                        stH264QVbr.u32TargetBitRate = 1024 + 512*u32FrameRate/30;
                        break;
                    case PIC_360P:
                        stH264QVbr.u32TargetBitRate = 1024 * 2   + 1024*u32FrameRate/30;
                        break;
                    case PIC_720P:
                        stH264QVbr.u32TargetBitRate = 1024 * 2   + 1024*u32FrameRate/30;
                        break;
                    case PIC_1080P:
                        stH264QVbr.u32TargetBitRate = 1024 * 2   + 2048*u32FrameRate/30;
                        break;
                    case PIC_2592x1944:
                        stH264QVbr.u32TargetBitRate = 1024 * 3   + 3072*u32FrameRate/30;
                        break;
                    case PIC_3840x2160:
                        stH264QVbr.u32TargetBitRate = 1024 * 5   + 5120*u32FrameRate/30;
                        break;
                    case PIC_4000x3000:
                        stH264QVbr.u32TargetBitRate = 1024 * 10  + 5120*u32FrameRate/30;
                        break;
                    case PIC_7680x4320:
                        stH264QVbr.u32TargetBitRate = 1024 * 20  + 5120*u32FrameRate/30;
                        break;
                    default :
                        stH264QVbr.u32TargetBitRate = 1024 * 15  + 2048*u32FrameRate/30;
                        break;
                }
                memcpy(&stVencChnAttr.stRcAttr.stH264QVbr, &stH264QVbr, sizeof(VENC_H264_QVBR_S));
            }
            else if(HIMPP_RC_CVBR == enRcMode)
            {
                VENC_H264_CVBR_S    stH264CVbr;

                stVencChnAttr.stRcAttr.enRcMode = VENC_RC_MODE_H264CVBR;
                stH264CVbr.u32Gop         = u32Gop;
                stH264CVbr.u32StatTime    = u32StatTime;
                stH264CVbr.u32SrcFrameRate  = u32FrameRate;
                stH264CVbr.fr32DstFrameRate = u32FrameRate;
                stH264CVbr.u32LongTermStatTime  = 1;
                stH264CVbr.u32ShortTermStatTime = u32StatTime;
                switch (enSize)
                {
                    case PIC_VGA:
                        stH264CVbr.u32MaxBitRate         = 1024 + 512*u32FrameRate/30;
                        stH264CVbr.u32LongTermMaxBitrate = 1024 + 512*u32FrameRate/30;
                        stH264CVbr.u32LongTermMinBitrate = 256;
                        break;
                    case PIC_720P:
                        stH264CVbr.u32MaxBitRate         = 1024 * 3 + 1024*u32FrameRate/30;
                        stH264CVbr.u32LongTermMaxBitrate = 1024 * 2 + 1024*u32FrameRate/30;
                        stH264CVbr.u32LongTermMinBitrate = 512;
                        break;
                    case PIC_1080P:
                        stH264CVbr.u32MaxBitRate         = 1024 * 2 + 2048*u32FrameRate/30;
                        stH264CVbr.u32LongTermMaxBitrate = 1024 * 2 + 2048*u32FrameRate/30;
                        stH264CVbr.u32LongTermMinBitrate = 1024;
                        break;
                    case PIC_2592x1944:
                        stH264CVbr.u32MaxBitRate         = 1024 * 4 + 3072*u32FrameRate/30;
                        stH264CVbr.u32LongTermMaxBitrate = 1024 * 3 + 3072*u32FrameRate/30;
                        stH264CVbr.u32LongTermMinBitrate = 1024*2;
                        break;
                    case PIC_3840x2160:
                        stH264CVbr.u32MaxBitRate         = 1024 * 8  + 5120*u32FrameRate/30;
                        stH264CVbr.u32LongTermMaxBitrate = 1024 * 5  + 5120*u32FrameRate/30;
                        stH264CVbr.u32LongTermMinBitrate = 1024*3;
                        break;
                    case PIC_4000x3000:
                        stH264CVbr.u32MaxBitRate         = 1024 * 12  + 5120*u32FrameRate/30;
                        stH264CVbr.u32LongTermMaxBitrate = 1024 * 10 + 5120*u32FrameRate/30;
                        stH264CVbr.u32LongTermMinBitrate = 1024*4;
                        break;
                    case PIC_7680x4320:
                        stH264CVbr.u32MaxBitRate         = 1024 * 24  + 5120*u32FrameRate/30;
                        stH264CVbr.u32LongTermMaxBitrate = 1024 * 20 + 5120*u32FrameRate/30;
                        stH264CVbr.u32LongTermMinBitrate = 1024*6;
                        break;
                    default :
                        stH264CVbr.u32MaxBitRate         = 1024 * 24  + 5120*u32FrameRate/30;
                        stH264CVbr.u32LongTermMaxBitrate = 1024 * 15 + 2048*u32FrameRate/30;
                        stH264CVbr.u32LongTermMinBitrate = 1024*5;
                        break;
                }
                memcpy(&stVencChnAttr.stRcAttr.stH264CVbr, &stH264CVbr, sizeof(VENC_H264_CVBR_S));
            }
            else if(HIMPP_RC_QPMAP == enRcMode)
            {
                VENC_H264_QPMAP_S    stH264QpMap;

                stVencChnAttr.stRcAttr.enRcMode = VENC_RC_MODE_H264QPMAP;
                stH264QpMap.u32Gop           = u32Gop;
                stH264QpMap.u32StatTime      = u32StatTime;
                stH264QpMap.u32SrcFrameRate  = u32FrameRate;
                stH264QpMap.fr32DstFrameRate = u32FrameRate;
                memcpy(&stVencChnAttr.stRcAttr.stH264QpMap, &stH264QpMap, sizeof(VENC_H264_QPMAP_S));
            }
            else
            {
                HIMPP_PRT("%s,%d,enRcMode(%d) not support\n",__FUNCTION__,__LINE__,enRcMode);
                return HI_FAILURE;
            }
            stVencChnAttr.stVencAttr.stAttrH264e.bRcnRefShareBuf = bRcnRefShareBuf;
        }
        break;
        case PT_MJPEG:
        {
            if (HIMPP_RC_FIXQP == enRcMode)
            {
                VENC_MJPEG_FIXQP_S stMjpegeFixQp;

                stVencChnAttr.stRcAttr.enRcMode = VENC_RC_MODE_MJPEGFIXQP;
                stMjpegeFixQp.u32Qfactor        = 95;
                stMjpegeFixQp.u32SrcFrameRate    = u32FrameRate;
                stMjpegeFixQp.fr32DstFrameRate   = u32FrameRate;

                memcpy(&stVencChnAttr.stRcAttr.stMjpegFixQp, &stMjpegeFixQp,sizeof(VENC_MJPEG_FIXQP_S));
            }
            else if (HIMPP_RC_CBR == enRcMode)
            {
                VENC_MJPEG_CBR_S stMjpegeCbr;

                stVencChnAttr.stRcAttr.enRcMode = VENC_RC_MODE_MJPEGCBR;
                stMjpegeCbr.u32StatTime         = u32StatTime;
                stMjpegeCbr.u32SrcFrameRate     = u32FrameRate;
                stMjpegeCbr.fr32DstFrameRate    = u32FrameRate;
                switch (enSize)
                {
                     case PIC_VGA:
                        stMjpegeCbr.u32BitRate = 1024 * 3  + 1024*u32FrameRate/30;
                        break;
                    case PIC_720P:
                        stMjpegeCbr.u32BitRate = 1024 * 5  + 1024*u32FrameRate/30;
                        break;
                    case PIC_1080P:
                        stMjpegeCbr.u32BitRate = 1024 * 8  + 2048*u32FrameRate/30;
                        break;
                    case PIC_2592x1944:
                        stMjpegeCbr.u32BitRate = 1024 * 20 + 3072*u32FrameRate/30;
                        break;
                    case PIC_3840x2160:
                        stMjpegeCbr.u32BitRate = 1024 * 25 + 5120*u32FrameRate/30;
                        break;
                    case PIC_4000x3000:
                        stMjpegeCbr.u32BitRate = 1024 * 30 + 5120*u32FrameRate/30;
                        break;
                    case PIC_7680x4320:
                        stMjpegeCbr.u32BitRate = 1024 * 40 + 5120*u32FrameRate/30;
                        break;
                    default :
                        stMjpegeCbr.u32BitRate = 1024 * 20 + 2048*u32FrameRate/30;
                        break;
                }

                memcpy(&stVencChnAttr.stRcAttr.stMjpegCbr, &stMjpegeCbr,sizeof(VENC_MJPEG_CBR_S));
            }
            else if (HIMPP_RC_VBR == enRcMode)
            {
                VENC_MJPEG_VBR_S   stMjpegVbr;

                stVencChnAttr.stRcAttr.enRcMode = VENC_RC_MODE_MJPEGVBR;
                stMjpegVbr.u32StatTime      = u32StatTime;
                stMjpegVbr.u32SrcFrameRate  = u32FrameRate;
                stMjpegVbr.fr32DstFrameRate = 5;

                switch (enSize)
                {
                    case PIC_VGA:
                        stMjpegVbr.u32MaxBitRate = 1024 * 3  + 1024*u32FrameRate/30;
                        break;
                    case PIC_720P:
                        stMjpegVbr.u32MaxBitRate = 1024 * 5 + 1024*u32FrameRate/30;
                        break;
                    case PIC_1080P:
                        stMjpegVbr.u32MaxBitRate = 1024 * 8 + 2048*u32FrameRate/30;
                        break;
                    case PIC_2592x1944:
                        stMjpegVbr.u32MaxBitRate = 1024 * 20 + 3072*u32FrameRate/30;
                        break;
                    case PIC_3840x2160:
                        stMjpegVbr.u32MaxBitRate = 1024 * 25 + 5120*u32FrameRate/30;
                        break;
                    case PIC_4000x3000:
                        stMjpegVbr.u32MaxBitRate    = 1024 * 30 + 5120*u32FrameRate/30;
                        break;
                    case PIC_7680x4320:
                        stMjpegVbr.u32MaxBitRate = 1024 * 40 + 5120*u32FrameRate/30;
                        break;
                    default :
                        stMjpegVbr.u32MaxBitRate = 1024 * 20 + 2048*u32FrameRate/30;
                        break;
                }

                memcpy(&stVencChnAttr.stRcAttr.stMjpegVbr, &stMjpegVbr,sizeof(VENC_MJPEG_VBR_S));
            }
            else
            {
                HIMPP_PRT("cann't support other mode(%d) in this version!\n",enRcMode);
                return HI_FAILURE;
            }
        }
        break;

        case PT_JPEG:
            stJpegAttr.bSupportDCF                  = HI_FALSE;
            stJpegAttr.stMPFCfg.u8LargeThumbNailNum = 0;
            stJpegAttr.enReceiveMode                = VENC_PIC_RECEIVE_SINGLE;
            memcpy(&stVencChnAttr.stVencAttr.stAttrJpege, &stJpegAttr, sizeof(VENC_ATTR_JPEG_S));
            break;
        default:
            HIMPP_PRT("cann't support this enType (%d) in this version!\n",enType);
            return HI_ERR_VENC_NOT_SUPPORT;
    }

    if(PT_MJPEG == enType || PT_JPEG == enType )
    {
        stVencChnAttr.stGopAttr.enGopMode  = VENC_GOPMODE_NORMALP;
        stVencChnAttr.stGopAttr.stNormalP.s32IPQpDelta = 0;
    }
    else
    {
        memcpy(&stVencChnAttr.stGopAttr,pstGopAttr,sizeof(VENC_GOP_ATTR_S));
        if((VENC_GOPMODE_BIPREDB == pstGopAttr->enGopMode)&&(PT_H264 == enType))
        {
            if(0 == stVencChnAttr.stVencAttr.u32Profile)
            {
                stVencChnAttr.stVencAttr.u32Profile = 1;

                HIMPP_PRT("H.264 base profile not support BIPREDB, so change profile to main profile!\n");
            }
        }

        if((VENC_RC_MODE_H264QPMAP == stVencChnAttr.stRcAttr.enRcMode)||(VENC_RC_MODE_H265QPMAP == stVencChnAttr.stRcAttr.enRcMode))
        {
            if(VENC_GOPMODE_ADVSMARTP == pstGopAttr->enGopMode)
            {
                stVencChnAttr.stGopAttr.enGopMode = VENC_GOPMODE_SMARTP;

                HIMPP_PRT("advsmartp not support QPMAP, so change gopmode to smartp!\n");
            }
        }
    }

    s32Ret = HI_MPI_VENC_CreateChn(VencChn, &stVencChnAttr);
    if (HI_SUCCESS != s32Ret)
    {
        HIMPP_PRT("HI_MPI_VENC_CreateChn [%d] faild with %#x! ===\n", \
                   VencChn, s32Ret);
        return s32Ret;
    }

    s32Ret = HIMPP_VENC_CloseReEncode(VencChn);
    if (HI_SUCCESS != s32Ret)
    {
        HI_MPI_VENC_DestroyChn(VencChn);
        return s32Ret;
    }

    return HI_SUCCESS;
}


/******************************************************************************
* funciton : Start venc stream mode
* note      : rate control parameter need adjust, according your case.
******************************************************************************/
HI_S32 HIMPP_VENC_Start(VENC_CHN VencChn, PAYLOAD_TYPE_E enType,  PIC_SIZE_E enSize, HIMPP_RC_E enRcMode, HI_U32  u32Profile, HI_BOOL bRcnRefShareBuf,VENC_GOP_ATTR_S *pstGopAttr)
{
    HI_S32 s32Ret;
    VENC_RECV_PIC_PARAM_S  stRecvParam;

    /******************************************
     step 1:  Creat Encode Chnl
    ******************************************/
    s32Ret = HIMPP_VENC_Creat(VencChn,enType,enSize,enRcMode,u32Profile,bRcnRefShareBuf,pstGopAttr);
    if (HI_SUCCESS != s32Ret)
    {
        HIMPP_PRT("HIMPP_VENC_Creat faild with%#x! \n", s32Ret);
        return HI_FAILURE;
    }
    /******************************************
     step 2:  Start Recv Venc Pictures
    ******************************************/
    stRecvParam.s32RecvPicNum = -1;
    s32Ret = HI_MPI_VENC_StartRecvFrame(VencChn,&stRecvParam);
    if (HI_SUCCESS != s32Ret)
    {
        HIMPP_PRT("HI_MPI_VENC_StartRecvPic faild with%#x! \n", s32Ret);
        return HI_FAILURE;
    }
    return HI_SUCCESS;
}

/******************************************************************************
* funciton : Stop venc ( stream mode -- H264, MJPEG )
******************************************************************************/
HI_S32 HIMPP_VENC_Stop(VENC_CHN VencChn)
{
    HI_S32 s32Ret;
    /******************************************
     step 1:  Stop Recv Pictures
    ******************************************/
    s32Ret = HI_MPI_VENC_StopRecvFrame(VencChn);
    if (HI_SUCCESS != s32Ret)
    {
        HIMPP_PRT("HI_MPI_VENC_StopRecvPic vechn[%d] failed with %#x!\n", \
                   VencChn, s32Ret);
        return HI_FAILURE;
    }    /******************************************
     step 2:  Distroy Venc Channel
    ******************************************/
    s32Ret = HI_MPI_VENC_DestroyChn(VencChn);
    if (HI_SUCCESS != s32Ret)
    {
        HIMPP_PRT("HI_MPI_VENC_DestroyChn vechn[%d] failed with %#x!\n", \
                   VencChn, s32Ret);
        return HI_FAILURE;
    }
    return HI_SUCCESS;
}

/******************************************************************************
* funciton : Start snap
******************************************************************************/

HI_S32 HIMPP_VENC_SnapStart(VENC_CHN VencChn, SIZE_S* pstSize, HI_BOOL bSupportDCF)
{
    HI_S32 s32Ret;
    VENC_CHN_ATTR_S stVencChnAttr;
    /******************************************
     step 1:  Create Venc Channel
    ******************************************/
    stVencChnAttr.stVencAttr.enType = PT_JPEG;
    stVencChnAttr.stVencAttr.u32MaxPicWidth     = pstSize->u32Width;
    stVencChnAttr.stVencAttr.u32MaxPicHeight    = pstSize->u32Height;
    stVencChnAttr.stVencAttr.u32PicWidth        = pstSize->u32Width;
    stVencChnAttr.stVencAttr.u32PicHeight       = pstSize->u32Height;
    stVencChnAttr.stVencAttr.u32BufSize         = ALIGN_UP(pstSize->u32Width, 16) * ALIGN_UP(pstSize->u32Height, 16);
    stVencChnAttr.stVencAttr.bByFrame           = HI_TRUE;/*get stream mode is field mode  or frame mode*/
    stVencChnAttr.stVencAttr.stAttrJpege.bSupportDCF = bSupportDCF;
    //stVencChnAttr.stVencAttr.stAttrJpege.bSupportXMP = HI_FALSE;
    stVencChnAttr.stVencAttr.stAttrJpege.stMPFCfg.u8LargeThumbNailNum = 0;
    stVencChnAttr.stVencAttr.stAttrJpege.enReceiveMode                = VENC_PIC_RECEIVE_SINGLE;
    stVencChnAttr.stVencAttr.u32Profile = 0;

    s32Ret = HI_MPI_VENC_CreateChn(VencChn, &stVencChnAttr);
    if (HI_SUCCESS != s32Ret)
    {
        HIMPP_PRT("HI_MPI_VENC_CreateChn [%d] faild with %#x!\n", \
                   VencChn, s32Ret);
        return s32Ret;
    }
    return HI_SUCCESS;
}

/******************************************************************************
* funciton : Stop snap
******************************************************************************/
HI_S32 HIMPP_VENC_SnapStop(VENC_CHN VencChn)
{
    HI_S32 s32Ret;
    s32Ret = HI_MPI_VENC_StopRecvFrame(VencChn);
    if (HI_SUCCESS != s32Ret)
    {
        HIMPP_PRT("HI_MPI_VENC_StopRecvPic vechn[%d] failed with %#x!\n", VencChn, s32Ret);
        return HI_FAILURE;
    }
    s32Ret = HI_MPI_VENC_DestroyChn(VencChn);
    if (HI_SUCCESS != s32Ret)
    {
        HIMPP_PRT("HI_MPI_VENC_DestroyChn vechn[%d] failed with %#x!\n", VencChn, s32Ret);
        return HI_FAILURE;
    }
    return HI_SUCCESS;
}

/******************************************************************************
* funciton : snap process
******************************************************************************/

HI_S32 HIMPP_VENC_SnapProcess(VENC_CHN VencChn, HI_U32 SnapCnt, HI_BOOL bSaveJpg, HI_BOOL bSaveThm)
{
    struct timeval TimeoutVal;
    fd_set read_fds;
    HI_S32 s32VencFd;
    VENC_CHN_STATUS_S stStat;
    VENC_STREAM_S stStream;
    HI_S32 s32Ret;
    VENC_RECV_PIC_PARAM_S  stRecvParam;
    MPP_CHN_S stDestChn;
    MPP_CHN_S stSrcChn;
    VPSS_CHN_ATTR_S stVpssChnAttr;
    HI_U32 i;

#ifdef __HuaweiLite__
    VENC_STREAM_BUF_INFO_S  stStreamBufInfo;
#endif

    /******************************************
     step 2:  Start Recv Venc Pictures
    ******************************************/
    stRecvParam.s32RecvPicNum = SnapCnt;
    s32Ret = HI_MPI_VENC_StartRecvFrame(VencChn, &stRecvParam);
    if (HI_SUCCESS != s32Ret)
    {
        HIMPP_PRT("HI_MPI_VENC_StartRecvPic faild with%#x!\n", s32Ret);
        return HI_FAILURE;
    }

    /******************************************
     step 3:  Start Recv Venc Pictures
    ******************************************/
    stDestChn.enModId  = HI_ID_VENC;
    stDestChn.s32DevId = 0;
    stDestChn.s32ChnId = VencChn;
    s32Ret = HI_MPI_SYS_GetBindbyDest(&stDestChn, &stSrcChn);
    if (s32Ret == HI_SUCCESS && stSrcChn.enModId == HI_ID_VPSS)
    {
        s32Ret = HI_MPI_VPSS_GetChnAttr(stSrcChn.s32DevId, stSrcChn.s32ChnId, &stVpssChnAttr);
        if (s32Ret == HI_SUCCESS && stVpssChnAttr.enCompressMode != COMPRESS_MODE_NONE)
        {
            s32Ret = HI_MPI_VPSS_TriggerSnapFrame(stSrcChn.s32DevId, stSrcChn.s32ChnId, SnapCnt);
            if (s32Ret != HI_SUCCESS)
            {
                HIMPP_PRT("call HI_MPI_VPSS_TriggerSnapFrame Grp = %d, ChanId = %d, SnapCnt = %d return failed(0x%x)!\n",
                    stSrcChn.s32DevId, stSrcChn.s32ChnId, SnapCnt, s32Ret);

                return HI_FAILURE;
            }
        }
    }

    /******************************************
     step 4:  recv picture
    ******************************************/
    s32VencFd = HI_MPI_VENC_GetFd(VencChn);
    if (s32VencFd < 0)
    {
        HIMPP_PRT("HI_MPI_VENC_GetFd faild with%#x!\n", s32VencFd);
        return HI_FAILURE;
    }

    for(i=0; i<SnapCnt; i++)
    {
        FD_ZERO(&read_fds);
        FD_SET(s32VencFd, &read_fds);
        TimeoutVal.tv_sec  = 10;
        TimeoutVal.tv_usec = 0;
        s32Ret = select(s32VencFd + 1, &read_fds, NULL, NULL, &TimeoutVal);
        if (s32Ret < 0)
        {
            HIMPP_PRT("snap select failed!\n");
            return HI_FAILURE;
        }
        else if (0 == s32Ret)
        {
            HIMPP_PRT("snap time out!\n");
            return HI_FAILURE;
        }
        else
        {
            if (FD_ISSET(s32VencFd, &read_fds))
            {
                s32Ret = HI_MPI_VENC_QueryStatus(VencChn, &stStat);
                if (s32Ret != HI_SUCCESS)
                {
                    HIMPP_PRT("HI_MPI_VENC_QueryStatus failed with %#x!\n", s32Ret);
                    return HI_FAILURE;
                }
                /*******************************************************
                suggest to check both u32CurPacks and u32LeftStreamFrames at the same time,for example:
                 if(0 == stStat.u32CurPacks || 0 == stStat.u32LeftStreamFrames)
                 {                HIMPP_PRT("NOTE: Current  frame is NULL!\n");
                    return HI_SUCCESS;
                 }
                 *******************************************************/
                if (0 == stStat.u32CurPacks)
                {
                    HIMPP_PRT("NOTE: Current  frame is NULL!\n");
                    return HI_SUCCESS;
                }
                stStream.pstPack = (VENC_PACK_S*)malloc(sizeof(VENC_PACK_S) * stStat.u32CurPacks);
                if (NULL == stStream.pstPack)
                {
                    HIMPP_PRT("malloc memory failed!\n");
                    return HI_FAILURE;
                }
                stStream.u32PackCount = stStat.u32CurPacks;
                s32Ret = HI_MPI_VENC_GetStream(VencChn, &stStream, -1);
                if (HI_SUCCESS != s32Ret)
                {
                    HIMPP_PRT("HI_MPI_VENC_GetStream failed with %#x!\n", s32Ret);

                    free(stStream.pstPack);
                    stStream.pstPack = NULL;
                    return HI_FAILURE;
                }
                if(bSaveJpg || bSaveThm)
                {
                    char acFile[FILE_NAME_LEN]    = {0};
                    FILE* pFile;

                    snprintf(acFile, FILE_NAME_LEN, "snap_%d.jpg", gs_s32SnapCnt);
                    pFile = fopen(acFile, "wb");
                    if (pFile == NULL)
                    {
                        HIMPP_PRT("open file err\n");

                        free(stStream.pstPack);
                        stStream.pstPack = NULL;
                        return HI_FAILURE;
                    }
#ifndef __HuaweiLite__
                    s32Ret = HIMPP_VENC_SaveStream(pFile, &stStream);
                    if (HI_SUCCESS != s32Ret)
                    {
                        HIMPP_PRT("save snap picture failed!\n");

                        free(stStream.pstPack);
                        stStream.pstPack = NULL;

                        fclose(pFile);
                        return HI_FAILURE;
                    }

#else
                    s32Ret = HI_MPI_VENC_GetStreamBufInfo (VencChn, &stStreamBufInfo);
                    if (HI_SUCCESS != s32Ret)
                    {
                        HIMPP_PRT("HI_MPI_VENC_GetStreamBufInfo failed with %#x!\n", s32Ret);

                        free(stStream.pstPack);
                        stStream.pstPack = NULL;

                        fclose(pFile);
                        return HI_FAILURE;
                    }

                    s32Ret = HIMPP_VENC_SaveStream_PhyAddr(pFile, &stStreamBufInfo, &stStream);
                    if (HI_SUCCESS != s32Ret)
                    {
                        HIMPP_PRT("save snap picture failed!\n");

                        free(stStream.pstPack);
                        stStream.pstPack = NULL;

                        fclose(pFile);
                        return HI_FAILURE;
                    }
#endif
                    if(bSaveThm)
                    {
                        char acFile_dcf[FILE_NAME_LEN]  = {0};
                        snprintf(acFile_dcf, FILE_NAME_LEN, "snap_thm_%d.jpg", gs_s32SnapCnt);
                        s32Ret = HIMPP_VENC_Getdcfinfo(acFile, acFile_dcf);
                        if (HI_SUCCESS != s32Ret)
                        {
                            HIMPP_PRT("save thm picture failed!\n");

                            free(stStream.pstPack);
                            stStream.pstPack = NULL;

                            fclose(pFile);
                            return HI_FAILURE;
                        }
                    }

                    fclose(pFile);
                    gs_s32SnapCnt++;
                }

                s32Ret = HI_MPI_VENC_ReleaseStream(VencChn, &stStream);
                if (HI_SUCCESS != s32Ret)
                {
                    HIMPP_PRT("HI_MPI_VENC_ReleaseStream failed with %#x!\n", s32Ret);

                    free(stStream.pstPack);
                    stStream.pstPack = NULL;

                    return HI_FAILURE;
                }

                free(stStream.pstPack);
                stStream.pstPack = NULL;
            }
        }
    }
    /******************************************
     step 5:  stop recv picture
    ******************************************/
    s32Ret = HI_MPI_VENC_StopRecvFrame(VencChn);
    if (s32Ret != HI_SUCCESS)
    {
        HIMPP_PRT("HI_MPI_VENC_StopRecvPic failed with %#x!\n",  s32Ret);
        return HI_FAILURE;
    }
    return HI_SUCCESS;
}

HI_S32 HIMPP_VENC_SaveJpeg(VENC_CHN VencChn, HI_U32 SnapCnt)
{
    struct timeval TimeoutVal;
    fd_set read_fds;
    HI_S32 s32VencFd;
    VENC_CHN_STATUS_S stStat;
    VENC_STREAM_S stStream;
    HI_S32 s32Ret;
    HI_U32 i;

#ifdef __HuaweiLite__
    VENC_STREAM_BUF_INFO_S  stStreamBufInfo;
#endif

    s32VencFd = HI_MPI_VENC_GetFd(VencChn);
    if (s32VencFd < 0)
    {
        HIMPP_PRT("HI_MPI_VENC_GetFd faild with%#x!\n", s32VencFd);
        return HI_FAILURE;
    }

    for(i=0; i<SnapCnt; i++)
    {
        FD_ZERO(&read_fds);
        FD_SET(s32VencFd, &read_fds);
        TimeoutVal.tv_sec  = 10;
        TimeoutVal.tv_usec = 0;
        s32Ret = select(s32VencFd + 1, &read_fds, NULL, NULL, &TimeoutVal);
        if (s32Ret < 0)
        {
            HIMPP_PRT("snap select failed!\n");
            return HI_FAILURE;
        }
        else if (0 == s32Ret)
        {
            HIMPP_PRT("snap time out!\n");
            return HI_FAILURE;
        }
        else
        {
            if (FD_ISSET(s32VencFd, &read_fds))
            {
                s32Ret = HI_MPI_VENC_QueryStatus(VencChn, &stStat);
                if (s32Ret != HI_SUCCESS)
                {
                    HIMPP_PRT("HI_MPI_VENC_QueryStatus failed with %#x!\n", s32Ret);
                    return HI_FAILURE;
                }
                /*******************************************************
                suggest to check both u32CurPacks and u32LeftStreamFrames at the same time,for example:
                 if(0 == stStat.u32CurPacks || 0 == stStat.u32LeftStreamFrames)
                 {                HIMPP_PRT("NOTE: Current  frame is NULL!\n");
                    return HI_SUCCESS;
                 }
                 *******************************************************/
                if (0 == stStat.u32CurPacks)
                {
                    HIMPP_PRT("NOTE: Current  frame is NULL!\n");
                    return HI_SUCCESS;
                }
                stStream.pstPack = (VENC_PACK_S*)malloc(sizeof(VENC_PACK_S) * stStat.u32CurPacks);
                if (NULL == stStream.pstPack)
                {
                    HIMPP_PRT("malloc memory failed!\n");
                    return HI_FAILURE;
                }
                stStream.u32PackCount = stStat.u32CurPacks;
                s32Ret = HI_MPI_VENC_GetStream(VencChn, &stStream, -1);
                if (HI_SUCCESS != s32Ret)
                {
                    HIMPP_PRT("HI_MPI_VENC_GetStream failed with %#x!\n", s32Ret);

                    free(stStream.pstPack);
                    stStream.pstPack = NULL;
                    return HI_FAILURE;
                }
                if(1)
                {
                    char acFile[FILE_NAME_LEN]    = {0};
                    FILE* pFile;

                    snprintf(acFile, FILE_NAME_LEN, "snap_%d.jpg", gs_s32SnapCnt);
                    pFile = fopen(acFile, "wb");
                    if (pFile == NULL)
                    {
                        HIMPP_PRT("open file err\n");

                        free(stStream.pstPack);
                        stStream.pstPack = NULL;
                        return HI_FAILURE;
                    }
#ifndef __HuaweiLite__
                    s32Ret = HIMPP_VENC_SaveStream(pFile, &stStream);
                    if (HI_SUCCESS != s32Ret)
                    {
                        HIMPP_PRT("save snap picture failed!\n");

                        free(stStream.pstPack);
                        stStream.pstPack = NULL;

                        fclose(pFile);
                        return HI_FAILURE;
                    }

#else
                    s32Ret = HI_MPI_VENC_GetStreamBufInfo (VencChn, &stStreamBufInfo);
                    if (HI_SUCCESS != s32Ret)
                    {
                        HIMPP_PRT("HI_MPI_VENC_GetStreamBufInfo failed with %#x!\n", s32Ret);

                        free(stStream.pstPack);
                        stStream.pstPack = NULL;

                        fclose(pFile);
                        return HI_FAILURE;
                    }

                    s32Ret = HIMPP_VENC_SaveStream_PhyAddr(pFile, &stStreamBufInfo, &stStream);
                    if (HI_SUCCESS != s32Ret)
                    {
                        HIMPP_PRT("save snap picture failed!\n");

                        free(stStream.pstPack);
                        stStream.pstPack = NULL;

                        fclose(pFile);
                        return HI_FAILURE;
                    }
#endif

                    fclose(pFile);
                    gs_s32SnapCnt++;
                }

                s32Ret = HI_MPI_VENC_ReleaseStream(VencChn, &stStream);
                if (HI_SUCCESS != s32Ret)
                {
                    HIMPP_PRT("HI_MPI_VENC_ReleaseStream failed with %#x!\n", s32Ret);

                    free(stStream.pstPack);
                    stStream.pstPack = NULL;

                    return HI_FAILURE;
                }

                free(stStream.pstPack);
                stStream.pstPack = NULL;
            }
        }
    }

    return HI_SUCCESS;
}


#define QpMapBufNum         8
#define VENC_QPMAP_MAX_CHN  2
HI_VOID* HIMPP_QpmapSendFrameProc(HI_VOID* p)
{
    HI_U32 i,j,FrmId;
    HI_S32 s32Ret;
    VIDEO_FRAME_INFO_S  *pstVideoFrame;
    USER_FRAME_INFO_S   stFrame[VENC_QPMAP_MAX_CHN][QpMapBufNum];
    HIMPP_VENC_QPMAP_SENDFRAME_PARA_S *pstPara;

    HI_U32   u32QpMapSize[VENC_QPMAP_MAX_CHN];
    HI_U64   u64QpMapPhyAddr[VENC_QPMAP_MAX_CHN][QpMapBufNum];
    HI_VOID* pQpMapVirAddr[VENC_QPMAP_MAX_CHN][QpMapBufNum];

    HI_U32   u32SkipWeightSize[VENC_QPMAP_MAX_CHN];
    HI_U64   u64SkipWeightPhyAddr[VENC_QPMAP_MAX_CHN][QpMapBufNum];
    HI_VOID* pSkipWeightVirAddr[VENC_QPMAP_MAX_CHN][QpMapBufNum];

    HI_U8 *pVirAddr;
    HI_U64 u64PhyAddr;
    HI_U8 *pVirAddrTemp;

    VPSS_CHN_ATTR_S  stChnAttr;
    VENC_CHN_ATTR_S  VencChnAttr;

    pstPara = (HIMPP_VENC_QPMAP_SENDFRAME_PARA_S*)p;

    if (pstPara->s32Cnt > VENC_QPMAP_MAX_CHN)
    {
        HIMPP_PRT("Current func'HIMPP_QpmapSendFrameProc' not support Venc channal num(%d) > %d\n",pstPara->s32Cnt,VENC_QPMAP_MAX_CHN);
        return NULL;
    }

    for (i = 0; i < pstPara->s32Cnt; i++)
    {
        HI_MPI_VENC_GetChnAttr(pstPara->VeChn[i],&VencChnAttr);

        u32QpMapSize[i]      = VENC_GetQpmapSize(pstPara->stSize[i].u32Width, pstPara->stSize[i].u32Height);
        u32SkipWeightSize[i] = VENC_GetSkipWeightSize(VencChnAttr.stVencAttr.enType,
                                                      pstPara->stSize[i].u32Width, pstPara->stSize[i].u32Height);

        /*alloc qpmap memory*/
        s32Ret = HI_MPI_SYS_MmzAlloc(&u64PhyAddr, (void**)&pVirAddr, NULL, HI_NULL, u32QpMapSize[i]*QpMapBufNum);
        if (HI_SUCCESS != s32Ret)
        {
            HIMPP_PRT("HI_MPI_SYS_MmzAlloc err:0x%x",s32Ret);
            goto error;
        }
        for (j = 0; j < QpMapBufNum; j++)
        {
            u64QpMapPhyAddr[i][j] = u64PhyAddr + j*u32QpMapSize[i];
            pQpMapVirAddr[i][j]   = pVirAddr + j*u32QpMapSize[i];
        }

        /*alloc skipWeight memory*/
        s32Ret = HI_MPI_SYS_MmzAlloc(&u64PhyAddr, (void**)&pVirAddr, NULL, HI_NULL, u32SkipWeightSize[i]*QpMapBufNum);
        if (HI_SUCCESS != s32Ret)
        {
            HIMPP_PRT("HI_MPI_SYS_MmzAlloc err:0x%x",s32Ret);
            goto error;
        }
        for (j = 0; j < QpMapBufNum; j++)
        {
            u64SkipWeightPhyAddr[i][j] = u64PhyAddr + j*u32SkipWeightSize[i];
            pSkipWeightVirAddr[i][j]   = pVirAddr + j*u32SkipWeightSize[i];
        }
    }

    /* set vpss buffer depth*/
    for (i = 0; i < pstPara->s32Cnt; i++)
    {
        s32Ret = HI_MPI_VPSS_GetChnAttr(pstPara->VpssGrp,pstPara->VpssChn[i],&stChnAttr);
        if (HI_SUCCESS != s32Ret)
        {
            HIMPP_PRT("HI_MPI_VPSS_GetChnAttr err:0x%x",s32Ret);
            goto error;
        }

        stChnAttr.u32Depth = 3;
        s32Ret = HI_MPI_VPSS_SetChnAttr(pstPara->VpssGrp,pstPara->VpssChn[i],&stChnAttr);
        if (HI_SUCCESS != s32Ret)
        {
            HIMPP_PRT("HI_MPI_VPSS_SetChnAttr err:0x%x",s32Ret);
            goto error;
        }
    }

    FrmId = 0;
    while(HI_TRUE == pstPara->bThreadStart)
    {
        for (i = 0; i < pstPara->s32Cnt; i++)
        {
            pstVideoFrame = &stFrame[i][FrmId].stUserFrame;
            s32Ret = HI_MPI_VPSS_GetChnFrame(pstPara->VpssGrp,pstPara->VpssChn[i],pstVideoFrame,1000);
            if (HI_SUCCESS != s32Ret)
            {
                HIMPP_PRT("HI_MPI_VPSS_GetChnFrame err:0x%x\n",s32Ret);
                continue;
            }

            pVirAddrTemp = (HI_U8 *)pQpMapVirAddr[i][FrmId];
            for (j = 0; j < u32QpMapSize[i]; j++)
            {
                *pVirAddrTemp = 0x5E;    //[7]:skip flag; [6]:QpType Flag; [5:0]:Qp value ==> Set absolute qp = 30
                pVirAddrTemp++;
            }

            pVirAddrTemp = (HI_U8 *)pSkipWeightVirAddr[i][FrmId];
            for (j = 0; j < u32SkipWeightSize[i]; j++)
            {
                *pVirAddrTemp = 0x88;  // inter block must be skip
                pVirAddrTemp++;
            }

            stFrame[i][FrmId].stUserRcInfo.bSkipWeightValid = 1;
            stFrame[i][FrmId].stUserRcInfo.u64SkipWeightPhyAddr = u64SkipWeightPhyAddr[i][FrmId];
            stFrame[i][FrmId].stUserRcInfo.bQpMapValid     = 1;
            stFrame[i][FrmId].stUserRcInfo.u64QpMapPhyAddr = u64QpMapPhyAddr[i][FrmId];
            stFrame[i][FrmId].stUserRcInfo.u32BlkStartQp   = 30;
            stFrame[i][FrmId].stUserRcInfo.enFrameType = VENC_FRAME_TYPE_NONE;

            s32Ret = HI_MPI_VENC_SendFrameEx(pstPara->VeChn[i], &stFrame[i][FrmId], -1);
            if(HI_SUCCESS != s32Ret)
            {
                HIMPP_PRT("HI_MPI_VENC_SendFrame err:0x%x\n",s32Ret);

                s32Ret = HI_MPI_VPSS_ReleaseChnFrame(pstPara->VpssGrp,pstPara->VpssChn[i],pstVideoFrame);
                if(HI_SUCCESS != s32Ret)
                {
                    HIMPP_PRT("HI_MPI_VPSS_ReleaseChnFrame err:0x%x",s32Ret);
                    goto error;
                }
                break;
            }

            s32Ret = HI_MPI_VPSS_ReleaseChnFrame(pstPara->VpssGrp,pstPara->VpssChn[i],pstVideoFrame);
            if(HI_SUCCESS != s32Ret)
            {
                HIMPP_PRT("HI_MPI_VPSS_ReleaseChnFrame err:0x%x",s32Ret);
                goto error;
            }

            FrmId++;
            if(FrmId >= QpMapBufNum)
            {
                FrmId = 0;
            }
        }
    }

error:
    for (i = 0; i < pstPara->s32Cnt; i++)
    {
        if (u64QpMapPhyAddr[i][0] != 0)
        {
            s32Ret = HI_MPI_SYS_MmzFree(u64QpMapPhyAddr[i][0], pQpMapVirAddr[i][0]);
            if(HI_SUCCESS != s32Ret)
            {
                HIMPP_PRT("HI_MPI_SYS_MmzFree err:0x%x",s32Ret);
            }
        }

        if (u64SkipWeightPhyAddr[i][0] != 0)
        {
            s32Ret = HI_MPI_SYS_MmzFree(u64SkipWeightPhyAddr[i][0], pSkipWeightVirAddr[i][0]);
            if(HI_SUCCESS != s32Ret)
            {
                HIMPP_PRT("HI_MPI_SYS_MmzFree err:0x%x",s32Ret);
            }
        }
    }

    return NULL;
}
HI_S32 HIMPP_VENC_QpmapSendFrame(VPSS_GRP VpssGrp,VPSS_CHN VpssChn[],VENC_CHN VeChn[],HI_S32 s32Cnt,SIZE_S stSize[])
{
    HI_S32 i;

    stQpMapSendFramePara.bThreadStart = HI_TRUE;
    stQpMapSendFramePara.VpssGrp = VpssGrp;
    stQpMapSendFramePara.s32Cnt  = s32Cnt;

    for(i=0; i<s32Cnt;i++)
    {
        stQpMapSendFramePara.VeChn[i]   = VeChn[i];
        stQpMapSendFramePara.VpssChn[i] = VpssChn[i];
        stQpMapSendFramePara.stSize[i]  = stSize[i];
    }

    return pthread_create(&gs_VencQpmapPid, 0, HIMPP_QpmapSendFrameProc, (HI_VOID*)&stQpMapSendFramePara);
}



/******************************************************************************
* funciton : get stream from each channels and save them
******************************************************************************/
HI_VOID* HIMPP_VENC_GetVencStreamProc(HI_VOID* p)
{
    HI_S32 i;
    HI_S32 s32ChnTotal;
    VENC_CHN_ATTR_S stVencChnAttr;
    HIMPP_VENC_GETSTREAM_PARA_S* pstPara;
    HI_S32 maxfd = 0;
    struct timeval TimeoutVal;
    fd_set read_fds;
    HI_U32 u32PictureCnt[VENC_MAX_CHN_NUM]={0};
    HI_S32 VencFd[VENC_MAX_CHN_NUM];
    HI_CHAR aszFileName[VENC_MAX_CHN_NUM][64];
    FILE* pFile[VENC_MAX_CHN_NUM];
    char szFilePostfix[10];
    VENC_CHN_STATUS_S stStat;
    VENC_STREAM_S stStream;
    HI_S32 s32Ret;
    VENC_CHN VencChn;
    PAYLOAD_TYPE_E enPayLoadType[VENC_MAX_CHN_NUM];
    VENC_STREAM_BUF_INFO_S stStreamBufInfo[VENC_MAX_CHN_NUM];

    prctl(PR_SET_NAME, "GetVencStream", 0,0,0);

    pstPara = (HIMPP_VENC_GETSTREAM_PARA_S*)p;
    s32ChnTotal = pstPara->s32Cnt;
    /******************************************
     step 1:  check & prepare save-file & venc-fd
    ******************************************/
    if (s32ChnTotal >= VENC_MAX_CHN_NUM)
    {
        HIMPP_PRT("input count invaild\n");
        return NULL;
    }
    for (i = 0; i < s32ChnTotal; i++)
    {
        /* decide the stream file name, and open file to save stream */
        VencChn = pstPara->VeChn[i];
        s32Ret = HI_MPI_VENC_GetChnAttr(VencChn, &stVencChnAttr);
        if (s32Ret != HI_SUCCESS)
        {
            HIMPP_PRT("HI_MPI_VENC_GetChnAttr chn[%d] failed with %#x!\n", \
                       VencChn, s32Ret);
            return NULL;
        }
        enPayLoadType[i] = stVencChnAttr.stVencAttr.enType;

        s32Ret = HIMPP_VENC_GetFilePostfix(enPayLoadType[i], szFilePostfix);
        if (s32Ret != HI_SUCCESS)
        {
            HIMPP_PRT("HIMPP_VENC_GetFilePostfix [%d] failed with %#x!\n", \
                       stVencChnAttr.stVencAttr.enType, s32Ret);
            return NULL;
        }
        // if(PT_JPEG != enPayLoadType[i])
        // {
        //     snprintf(aszFileName[i],32, "stream_chn%d%s", i, szFilePostfix);

        //     pFile[i] = fopen(aszFileName[i], "wb");
        //     if (!pFile[i])
        //     {
        //         HIMPP_PRT("open file[%s] failed!\n",
        //                    aszFileName[i]);
        //         return NULL;
        //     }
        // }
        /* Set Venc Fd. */
        VencFd[i] = HI_MPI_VENC_GetFd(VencChn);
        if (VencFd[i] < 0)
        {
            HIMPP_PRT("HI_MPI_VENC_GetFd failed with %#x!\n",
                       VencFd[i]);
            return NULL;
        }
        if (maxfd <= VencFd[i])
        {
            maxfd = VencFd[i];
        }

        s32Ret = HI_MPI_VENC_GetStreamBufInfo (VencChn, &stStreamBufInfo[i]);
        if (HI_SUCCESS != s32Ret)
        {
            HIMPP_PRT("HI_MPI_VENC_GetStreamBufInfo failed with %#x!\n", s32Ret);
            return (void *)HI_FAILURE;
        }
    }

    /******************************************
     step 2:  Start to get streams of each channel.
    ******************************************/
    while (HI_TRUE == pstPara->bThreadStart)
    {
        FD_ZERO(&read_fds);
        for (i = 0; i < s32ChnTotal; i++)
        {
            FD_SET(VencFd[i], &read_fds);
        }

        TimeoutVal.tv_sec  = 2;
        TimeoutVal.tv_usec = 0;
        s32Ret = select(maxfd + 1, &read_fds, NULL, NULL, &TimeoutVal);
        if (s32Ret < 0)
        {
            HIMPP_PRT("select failed!\n");
            break;
        }
        else if (s32Ret == 0)
        {
            HIMPP_PRT("get venc stream time out, exit thread\n");
            continue;
        }
        else
        {
            for (i = 0; i < s32ChnTotal; i++)
            {
                if (FD_ISSET(VencFd[i], &read_fds))
                {
                    /*******************************************************
                     step 2.1 : query how many packs in one-frame stream.
                    *******************************************************/
                    memset(&stStream, 0, sizeof(stStream));

                    VencChn = pstPara->VeChn[i];

                    s32Ret = HI_MPI_VENC_QueryStatus(VencChn, &stStat);
                    if (HI_SUCCESS != s32Ret)
                    {
                        HIMPP_PRT("HI_MPI_VENC_QueryStatus chn[%d] failed with %#x!\n", VencChn, s32Ret);
                        break;
                    }

                    /*******************************************************
                    step 2.2 :suggest to check both u32CurPacks and u32LeftStreamFrames at the same time,for example:
                     if(0 == stStat.u32CurPacks || 0 == stStat.u32LeftStreamFrames)
                     {
                        HIMPP_PRT("NOTE: Current  frame is NULL!\n");
                        continue;
                     }
                    *******************************************************/
                    if(0 == stStat.u32CurPacks)
                    {
                          HIMPP_PRT("NOTE: Current  frame is NULL!\n");
                          continue;
                    }
                    /*******************************************************
                     step 2.3 : malloc corresponding number of pack nodes.
                    *******************************************************/
                    stStream.pstPack = (VENC_PACK_S*)malloc(sizeof(VENC_PACK_S) * stStat.u32CurPacks);
                    if (NULL == stStream.pstPack)
                    {
                        HIMPP_PRT("malloc stream pack failed!\n");
                        break;
                    }

                    /*******************************************************
                     step 2.4 : call mpi to get one-frame stream
                    *******************************************************/
                    stStream.u32PackCount = stStat.u32CurPacks;
                    s32Ret = HI_MPI_VENC_GetStream(VencChn, &stStream, HI_TRUE);
                    if (HI_SUCCESS != s32Ret)
                    {
                        free(stStream.pstPack);
                        stStream.pstPack = NULL;
                        HIMPP_PRT("HI_MPI_VENC_GetStream failed with %#x!\n", \
                                   s32Ret);
                        break;
                    }

                    /*******************************************************
                     step 2.5 : save frame to file
                    *******************************************************/
                    if(PT_JPEG == enPayLoadType[i])
                    {
                        strcpy(szFilePostfix, ".jpg");
                        snprintf(aszFileName[i],32, "stream_chn%d_%d%s", VencChn, u32PictureCnt[i],szFilePostfix);
                        pFile[i] = fopen(aszFileName[i], "wb");
                        if (!pFile[i])
                        {
                            HIMPP_PRT("open file err!\n");
                            return NULL;
                        }
                    }

#ifndef __HuaweiLite__
                    // s32Ret = HIMPP_VENC_SaveStream(pFile[i], &stStream);
                    // my edit
                    get_hisi_video_frame(VencChn, &stStream);
#else
                    s32Ret = HIMPP_VENC_SaveStream_PhyAddr(pFile[i], &stStreamBufInfo[i], &stStream);
#endif
                    if (HI_SUCCESS != s32Ret)
                    {
                        free(stStream.pstPack);
                        stStream.pstPack = NULL;
                        HIMPP_PRT("save stream failed!\n");
                        break;
                    }
                    /*******************************************************
                     step 2.6 : release stream
                     *******************************************************/
                    s32Ret = HI_MPI_VENC_ReleaseStream(VencChn, &stStream);
                    if (HI_SUCCESS != s32Ret)
                    {
                        HIMPP_PRT("HI_MPI_VENC_ReleaseStream failed!\n");
                        free(stStream.pstPack);
                        stStream.pstPack = NULL;
                        break;
                    }

                    /*******************************************************
                     step 2.7 : free pack nodes
                    *******************************************************/
                    free(stStream.pstPack);
                    stStream.pstPack = NULL;
                    u32PictureCnt[i]++;
                    if(PT_JPEG == enPayLoadType[i])
                    {
                        fclose(pFile[i]);
                    }
                }
            }
        }
    }
    /*******************************************************
    * step 3 : close save-file
    *******************************************************/
    // for (i = 0; i < s32ChnTotal; i++)
    // {
    //     if(PT_JPEG != enPayLoadType[i])
    //     {
    //         fclose(pFile[i]);
    //     }
    // }
    return NULL;
}

/******************************************************************************
* funciton : start get venc stream process thread
******************************************************************************/
HI_S32 HIMPP_VENC_StartGetStream(VENC_CHN VeChn[],HI_S32 s32Cnt)
{
    HI_U32 i;

    gs_stPara.bThreadStart = HI_TRUE;
    gs_stPara.s32Cnt = s32Cnt;
    for(i=0; i<s32Cnt; i++)
    {
        gs_stPara.VeChn[i] = VeChn[i];
    }
    return pthread_create(&gs_VencPid, 0, HIMPP_VENC_GetVencStreamProc, (HI_VOID*)&gs_stPara);
}

/******************************************************************************
* funciton : stop get venc stream process.
******************************************************************************/
HI_S32 HIMPP_VENC_StopGetStream(void)
{
    if (HI_TRUE == gs_stPara.bThreadStart)
    {
        gs_stPara.bThreadStart = HI_FALSE;
        pthread_join(gs_VencPid, 0);
    }
    return HI_SUCCESS;
}

HI_S32 HIMPP_VENC_StopSendQpmapFrame(void)
{
    if (HI_TRUE == stQpMapSendFramePara.bThreadStart)
    {
        stQpMapSendFramePara.bThreadStart = HI_FALSE;
        pthread_join(gs_VencQpmapPid, 0);
    }
    return HI_SUCCESS;
}


HI_VOID HIMPP_VENC_ReadOneFrame( FILE* fp, HI_U8* pY, HI_U8* pU, HI_U8* pV,
                                       HI_U32 width, HI_U32 height, HI_U32 stride, HI_U32 stride2)
{
    HI_U8* pDst;
    HI_U32 u32Row;
    pDst = pY;
    for ( u32Row = 0; u32Row < height; u32Row++ )
    {
        fread( pDst, width, 1, fp );
        pDst += stride;
    }
    pDst = pU;
    for ( u32Row = 0; u32Row < height / 2; u32Row++ )
    {
        fread( pDst, width / 2, 1, fp );
        pDst += stride2;
    }
    pDst = pV;
    for ( u32Row = 0; u32Row < height / 2; u32Row++ )
    {
        fread( pDst, width / 2, 1, fp );
        pDst += stride2;
    }
}

HI_S32 HIMPP_VENC_PlanToSemi(HI_U8* pY, HI_S32 yStride,
                                   HI_U8* pU, HI_S32 uStride,
                                   HI_U8* pV, HI_S32 vStride,
                                   HI_S32 picWidth, HI_S32 picHeight)
{
    HI_S32 i;
    HI_U8* pTmpU, *ptu;
    HI_U8* pTmpV, *ptv;
    HI_S32 s32HafW = uStride >> 1 ;
    HI_S32 s32HafH = picHeight >> 1 ;
    HI_S32 s32Size = s32HafW * s32HafH;

    pTmpU = malloc( s32Size );
    if(pTmpU == HI_NULL)
    {
        printf("malloc buf failed\n");
        return HI_FAILURE;
    }
    ptu = pTmpU;

    pTmpV = malloc( s32Size );
    if (pTmpV == HI_NULL)
    {
        printf("malloc buf failed\n");
        free( pTmpU );
        return HI_FAILURE;
    }
    ptv = pTmpV;

    memcpy(pTmpU, pU, s32Size);
    memcpy(pTmpV, pV, s32Size);
    for (i = 0; i<s32Size >> 1; i++)
    {
        *pU++ = *pTmpV++;
        *pU++ = *pTmpU++;
    }
    for (i = 0; i<s32Size >> 1; i++)
    {
        *pV++ = *pTmpV++;
        *pV++ = *pTmpU++;
    }
    free( ptu );
    free( ptv );
    return HI_SUCCESS;
}

#ifdef __cplusplus
#if __cplusplus
}
#endif
#endif /* End of #ifdef __cplusplus */
