xnvi/action_2_poor/software/patches/kernel_patch/drivers/mtd/spi-nor/hisfc350/hisfc350_spi_ids.c

/*
 * Copyright (c) 2016 HiSilicon Technologies Co., Ltd.
 *
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
 */

#include "../spi_ids.h"

/*****************************************************************************/

#define SET_READ_STD(_dummy_, _size_, _clk_) \
    static struct spi_operation read_std_##_dummy_##_size_##_clk_ = { \
    SPI_IF_READ_STD, SPI_CMD_READ, _dummy_, _size_, _clk_ }

#define READ_STD(_dummy_, _size_, _clk_) read_std_##_dummy_##_size_##_clk_

#define SET_READ_FAST(_dummy_, _size_, _clk_) \
    static struct spi_operation read_fast_##_dummy_##_size_##_clk_ = { \
    SPI_IF_READ_FAST, SPI_CMD_FAST_READ, _dummy_, _size_, _clk_ }

#define READ_FAST(_dummy_, _size_, _clk_) read_fast_##_dummy_##_size_##_clk_

#define SET_READ_DUAL(_dummy_, _size_, _clk_) \
    static struct spi_operation read_dual_##_dummy_##_size_##_clk_ = { \
    SPI_IF_READ_DUAL, SPI_CMD_READ_DUAL, _dummy_, _size_, _clk_ }

#define READ_DUAL(_dummy_, _size_, _clk_) read_dual_##_dummy_##_size_##_clk_

#define SET_READ_QUAD(_dummy_, _size_, _clk_) \
    static struct spi_operation read_quad_##_dummy_##_size_##_clk_ = { \
    SPI_IF_READ_QUAD, SPI_CMD_READ_QUAD, _dummy_, _size_, _clk_ }

#define READ_QUAD(_dummy_, _size_, _clk_) read_quad_##_dummy_##_size_##_clk_

#define SET_READ_DUAL_ADDR(_dummy_, _size_, _clk_) \
    static struct spi_operation \
    read_dual_addr_##_dummy_##_size_##_clk_ = { \
    SPI_IF_READ_DUAL_ADDR, SPI_CMD_READ_DUAL_ADDR, _dummy_, _size_, _clk_ }

#define READ_DUAL_ADDR(_dummy_, _size_, _clk_) \
    read_dual_addr_##_dummy_##_size_##_clk_

#define SET_READ_QUAD_ADDR(_dummy_, _size_, _clk_) \
    static struct spi_operation \
    read_quad_addr_##_dummy_##_size_##_clk_ = { \
    SPI_IF_READ_QUAD_ADDR, SPI_CMD_READ_QUAD_ADDR, _dummy_, _size_, _clk_ }

#define READ_QUAD_ADDR(_dummy_, _size_, _clk_) \
    read_quad_addr_##_dummy_##_size_##_clk_

#define SET_WRITE_STD(_dummy_, _size_, _clk_) \
    static struct spi_operation write_std_##_dummy_##_size_##_clk_ = { \
    SPI_IF_WRITE_STD, SPI_CMD_PP, _dummy_, _size_, _clk_ }

#define WRITE_STD(_dummy_, _size_, _clk_) write_std_##_dummy_##_size_##_clk_

#define SET_WRITE_DUAL(_dummy_, _size_, _clk_) \
    static struct spi_operation write_dual_##_dummy_##_size_##_clk_ = { \
    SPI_IF_WRITE_DUAL, SPI_CMD_WRITE_DUAL, _dummy_, _size_, _clk_ }

#define WRITE_DUAL(_dummy_, _size_, _clk_) write_dual_##_dummy_##_size_##_clk_

#define SET_WRITE_QUAD(_dummy_, _size_, _clk_) \
    static struct spi_operation write_quad_##_dummy_##_size_##_clk_ = { \
    SPI_IF_WRITE_QUAD, SPI_CMD_WRITE_QUAD, _dummy_, _size_, _clk_ }

#define WRITE_QUAD(_dummy_, _size_, _clk_) \
    write_quad_##_dummy_##_size_##_clk_

#define SET_WRITE_DUAL_ADDR(_dummy_, _size_, _clk_) \
    static struct spi_operation \
    write_dual_addr_##_dummy_##_size_##_clk_ = { \
    SPI_IF_WRITE_DUAL_ADDR, SPI_CMD_WRITE_DUAL_ADDR,\
        _dummy_, _size_, _clk_ }

#define WRITE_DUAL_ADDR(_dummy_, _size_, _clk_) \
    write_dual_addr_##_dummy_##_size_##_clk_

#define SET_WRITE_QUAD_ADDR(_dummy_, _size_, _clk_) \
    static struct spi_operation \
    write_quad_addr_##_dummy_##_size_##_clk_ = { \
    SPI_IF_WRITE_QUAD_ADDR, SPI_CMD_WRITE_QUAD_ADDR, \
        _dummy_, _size_, _clk_ }

#define WRITE_QUAD_ADDR(_dummy_, _size_, _clk_) \
    write_quad_addr_##_dummy_##_size_##_clk_

#define SET_ERASE_SECTOR_4K(_dummy_, _size_, _clk_) \
    static struct spi_operation \
        erase_sector_4k_##_dummy_##_size_##_clk_ = { \
    SPI_IF_ERASE_SECTOR_4K, SPI_CMD_SE_4K, _dummy_, _size_, _clk_ }

#define ERASE_SECTOR_4K(_dummy_, _size_, _clk_) \
    erase_sector_4k_##_dummy_##_size_##_clk_
/*****************************************************************************/

#define SET_ERASE_SECTOR_32K(_dummy_, _size_, _clk_) \
    static struct spi_operation \
        erase_sector_32k_##_dummy_##_size_##_clk_ = { \
    SPI_IF_ERASE_SECTOR_32K, SPI_CMD_SE_32K, _dummy_, _size_, _clk_ }

#define ERASE_SECTOR_32K(_dummy_, _size_, _clk_) \
    erase_sector_32k_##_dummy_##_size_##_clk_
/*****************************************************************************/

#define SET_ERASE_SECTOR_64K(_dummy_, _size_, _clk_) \
    static struct spi_operation \
        erase_sector_64k_##_dummy_##_size_##_clk_ = { \
    SPI_IF_ERASE_SECTOR_64K, SPI_CMD_SE_64K, _dummy_, _size_, _clk_ }

#define ERASE_SECTOR_64K(_dummy_, _size_, _clk_) \
    erase_sector_64k_##_dummy_##_size_##_clk_

/*****************************************************************************/

#define SET_ERASE_SECTOR_256K(_dummy_, _size_, _clk_) \
    static struct spi_operation \
        erase_sector_256k_##_dummy_##_size_##_clk_ = { \
    SPI_IF_ERASE_SECTOR_256K, SPI_CMD_SE_256K, _dummy_, _size_, _clk_ }

#define ERASE_SECTOR_256K(_dummy_, _size_, _clk_) \
    erase_sector_256k_##_dummy_##_size_##_clk_
/*****************************************************************************/
SET_READ_STD(0, INFINITE, 0);
SET_READ_STD(0, INFINITE, 20);
SET_READ_STD(0, INFINITE, 32);
SET_READ_STD(0, INFINITE, 33);
SET_READ_STD(0, INFINITE, 40);
SET_READ_STD(0, INFINITE, 50);
SET_READ_STD(0, INFINITE, 54);
SET_READ_STD(0, INFINITE, 55);
SET_READ_STD(0, INFINITE, 66);

SET_READ_FAST(1, INFINITE, 50);
SET_READ_FAST(1, INFINITE, 64);
SET_READ_FAST(1, INFINITE, 66);
SET_READ_FAST(1, INFINITE, 75);
SET_READ_FAST(1, INFINITE, 80);
SET_READ_FAST(1, INFINITE, 86);
SET_READ_FAST(1, INFINITE, 100);
SET_READ_FAST(1, INFINITE, 104);
SET_READ_FAST(1, INFINITE, 108);
SET_READ_FAST(1, INFINITE, 133);

SET_READ_DUAL(1, INFINITE, 64);
SET_READ_DUAL(1, INFINITE, 75);
SET_READ_DUAL(1, INFINITE, 80);
SET_READ_DUAL(1, INFINITE, 84);
SET_READ_DUAL(1, INFINITE, 104);
SET_READ_DUAL(2, INFINITE, 104);
SET_READ_DUAL(1, INFINITE, 108);
SET_READ_DUAL(1, INFINITE, 133);

SET_READ_DUAL_ADDR(2, INFINITE, 64);
SET_READ_DUAL_ADDR(0, INFINITE, 80);
SET_READ_DUAL_ADDR(1, INFINITE, 80);
SET_READ_DUAL_ADDR(1, INFINITE, 84);
SET_READ_DUAL_ADDR(2, INFINITE, 84);
SET_READ_DUAL_ADDR(1, INFINITE, 104);
SET_READ_DUAL_ADDR(1, INFINITE, 108);
SET_READ_DUAL_ADDR(2, INFINITE, 133);

#ifndef CONFIG_CLOSE_SPI_8PIN_4IO
SET_READ_QUAD(1, INFINITE, 64);
SET_READ_QUAD(1, INFINITE, 80);
SET_READ_QUAD(1, INFINITE, 84);
SET_READ_QUAD(1, INFINITE, 104);
SET_READ_QUAD(1, INFINITE, 108);
SET_READ_QUAD(1, INFINITE, 133);

SET_READ_QUAD_ADDR(2, INFINITE, 80);
/* SET_READ_QUAD_ADDR(3, INFINITE, 50); */
SET_READ_QUAD_ADDR(3, INFINITE, 75);
SET_READ_QUAD_ADDR(3, INFINITE, 80);
SET_READ_QUAD_ADDR(5, INFINITE, 64);
SET_READ_QUAD_ADDR(5, INFINITE, 84);
SET_READ_QUAD_ADDR(3, INFINITE, 104);
SET_READ_QUAD_ADDR(3, INFINITE, 108);
SET_READ_QUAD_ADDR(5, INFINITE, 125);
#endif
/*****************************************************************************/
SET_WRITE_STD(0, 256, 0);
SET_WRITE_STD(0, 256, 33);
SET_WRITE_STD(0, 256, 50);
SET_WRITE_STD(0, 256, 64);
SET_WRITE_STD(0, 256, 66);
SET_WRITE_STD(0, 256, 75);
SET_WRITE_STD(0, 256, 80);
SET_WRITE_STD(0, 256, 86);
SET_WRITE_STD(0, 256, 100);
SET_WRITE_STD(0, 256, 104);
SET_WRITE_STD(0, 256, 108);
SET_WRITE_STD(0, 256, 133);

SET_WRITE_DUAL(0, 256, 64);
SET_WRITE_DUAL(0, 256, 75);
SET_WRITE_DUAL(0, 256, 108);
SET_WRITE_DUAL(0, 256, 133);

SET_WRITE_DUAL_ADDR(0, 256, 64);
SET_WRITE_DUAL_ADDR(0, 256, 75);
SET_WRITE_DUAL_ADDR(0, 256, 108);
SET_WRITE_DUAL_ADDR(0, 256, 133);

#ifndef CONFIG_CLOSE_SPI_8PIN_4IO
SET_WRITE_QUAD(0, 256, 64);
SET_WRITE_QUAD(0, 256, 80);
SET_WRITE_QUAD(0, 256, 108);
SET_WRITE_QUAD(0, 256, 133);

/* FIXME: As Micron MT25Q(and MIXC) and N25Q have different QUAD I/O write code,
 * but they have the same ID, so we cannot compatiable it. User can open
 * by theirselves. */
SET_WRITE_QUAD_ADDR(0, 256, 33);
/* SET_WRITE_QUAD_ADDR(0, 256, 64); */
SET_WRITE_QUAD_ADDR(0, 256, 104);
/* SET_WRITE_QUAD_ADDR(0, 256, 133); */
#endif
/*****************************************************************************/
SET_ERASE_SECTOR_32K(0, _32K, 0);

SET_ERASE_SECTOR_64K(0, _64K, 0);
SET_ERASE_SECTOR_64K(0, _64K, 33);
SET_ERASE_SECTOR_64K(0, _64K, 50);
SET_ERASE_SECTOR_64K(0, _64K, 64);
SET_ERASE_SECTOR_64K(0, _64K, 66);
SET_ERASE_SECTOR_64K(0, _64K, 75);
SET_ERASE_SECTOR_64K(0, _64K, 80);
SET_ERASE_SECTOR_64K(0, _64K, 86);
SET_ERASE_SECTOR_64K(0, _64K, 100);
SET_ERASE_SECTOR_64K(0, _64K, 104);
SET_ERASE_SECTOR_64K(0, _64K, 108);
SET_ERASE_SECTOR_64K(0, _64K, 133);

SET_ERASE_SECTOR_256K(0, _256K, 50);
SET_ERASE_SECTOR_256K(0, _256K, 104);

/*****************************************************************************/
#include "hisfc350_spi_general.c"
static struct spi_driver  spi_driver_general = {
    .wait_ready   = spi_general_wait_ready,
    .write_enable = spi_general_write_enable,
    .entry_4addr  = spi_general_entry_4addr,
    .bus_prepare  = spi_general_bus_prepare,
    .qe_enable = spi_general_qe_enable,
};

static struct spi_driver spi_driver_no_qe = {
    .wait_ready = spi_general_wait_ready,
    .write_enable = spi_general_write_enable,
    .entry_4addr = spi_general_entry_4addr,
    .bus_prepare  = spi_general_bus_prepare,
    .qe_enable = spi_do_not_qe_enable,
};

#include "hisfc350_spi_s25fl256s.c"
static struct spi_driver  spi_driver_s25fl256s = {
    .wait_ready   = spi_general_wait_ready,
    .write_enable = spi_general_write_enable,
    .entry_4addr  = spi_s25fl256s_entry_4addr,
    .bus_prepare  = spi_general_bus_prepare,
    .qe_enable = spi_general_qe_enable,
};

#include "hisfc350_spi_w25q256fv.c"
static struct spi_driver  spi_driver_w25q256fv = {
    .wait_ready   = spi_general_wait_ready,
    .write_enable = spi_general_write_enable,
    .entry_4addr  = spi_w25q256fv_entry_4addr,
    .bus_prepare  = spi_general_bus_prepare,
    .qe_enable = spi_general_qe_enable,
};

#include "hisfc350_spi_mx25l25635e.c"
static struct spi_driver  spi_driver_mx25l25635e = {
    .wait_ready   = spi_general_wait_ready,
    .write_enable = spi_general_write_enable,
    .entry_4addr  = spi_general_entry_4addr,
    .bus_prepare  = spi_general_bus_prepare,
    .qe_enable = spi_mx25l25635e_qe_enable,
};

static struct spi_driver  spi_driver_f25l64q = {
    .wait_ready   = spi_general_wait_ready,
    .write_enable = spi_general_write_enable,
    .entry_4addr  = spi_general_entry_4addr,
    .bus_prepare  = spi_general_bus_prepare,
    .qe_enable = spi_mx25l25635e_qe_enable,
};

#include "hisfc350_spi_gd25qxxx.c"
static struct spi_driver  spi_driver_gd25qxxx = {
    .wait_ready   = spi_general_wait_ready,
    .write_enable = spi_general_write_enable,
    .entry_4addr  = spi_general_entry_4addr,
    .bus_prepare  = spi_general_bus_prepare,
    .qe_enable = spi_gd25qxxx_qe_enable,
};

#include "hisfc350_spi_micron.c"
static struct spi_driver spi_driver_micron = {
    .wait_ready = spi_general_wait_ready,
    .write_enable = spi_general_write_enable,
    .entry_4addr = spi_micron_entry_4addr,
    .bus_prepare  = spi_general_bus_prepare,
    .qe_enable = spi_do_not_qe_enable,
};

/*****************************************************************************/
struct spi_info spi_info_table[] = {
    /* name        id                id_len chipsize(Bytes) erasesize */
    {
        "at25fs010",  {0x1f, 0x66, 0x01}, 3,  _128K,  _32K, 3,
        {
            &READ_STD(0, INFINITE, 0),
            0
        },
        {
            &WRITE_STD(0, 256, 0),
            0
        },
        {
            &ERASE_SECTOR_32K(0, _32K, 0),
            0
        },
        &spi_driver_general,
    },

    {
        "at25fs040",  {0x1f, 0x66, 0x04}, 3,  _512K,  _64K, 3,
        {
            &READ_STD(0, INFINITE, 0),
            0
        },
        {
            &WRITE_STD(0, 256, 0),
            0
        },
        {
            &ERASE_SECTOR_64K(0, _64K, 0),
            0
        },
        &spi_driver_general,
    },

    {
        "at25df041a", {0x1f, 0x44, 0x01}, 3,  _512K,  _64K, 3,
        {
            &READ_STD(0, INFINITE, 0),
            0
        },
        {
            &WRITE_STD(0, 256, 0),
            0
        },
        {
            &ERASE_SECTOR_64K(0, _64K, 0),
            0
        },
        &spi_driver_general,
    },

    {
        "at25df641",  {0x1f, 0x48, 0x00}, 3,  _8M,    _64K, 3,
        {
            &READ_STD(0, INFINITE, 0),
            0
        },
        {
            &WRITE_STD(0, 256, 0),
            0
        },
        {
            &ERASE_SECTOR_64K(0, _64K, 0),
            0
        },
        &spi_driver_general,
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
#endif
            0
        },
        {
            &WRITE_STD(0, 256, 108),
            0
        },
        {
            &ERASE_SECTOR_64K(0, _64K, 108),
            0
        },
        &spi_driver_general,
    },

    {0, {0}, 0, 0, 0, 0, {0}, {0}, {0}, NULL},
};
